zinkwazi/traffic-pcb-sb/software/esp-firmware/components/api_connect/test/resources/data_north_add_V2_0_0.csv

{https://bearanvil.com/current_data/data_north_V1_0_5.csv}
1 | 100
2 | 99
3 | 98
