zinkwazi/traffic-pcb-sb/software/server-software/test_data/missing_num.csv

LED Number | Freeway | Direction | Longitude | Latitude | Tile | openLr Code | Free Flow Speed | Reference
1 | 101 | North | 34.45745 | -119.980356 | 22/699279/1669046 | C6qyXxh+xwo7dOUMBr0KCA== | 72
1 | 101 | South | 34.45657 | -119.975818 | 22/699332/1669058 | C6qqoBiBTgooUhIs+XoKGg== | 73
2 | 101 | North | 34.440808 | -119.942794 | 22/699717/1669281 | C6q6qhh8Xwo5TO40BSkKCw== | 72
2 | 101 | South | 34.438392 | -119.928052 | 22/699888/1669315 | C6qzGBh+QwoqUxPP+5UKFw== | 73
3 | 101 | North | 0 | 0 | 0 | 0 | 0 | 2
3 | 101 | South | 0 | 0 | 0 | 0 | 0 | 2
4 | 101 | North | 34.432527 | -119.890335 | 22/700328/1669398 | C6rCBxh8lgo2QPA0/4sKCg== | 72
4 | 101 | South | 34.432419 | -119.881319 | 22/700433/1669399 | C6q8Uxh8NAooOg5WARAKFw== | 72
5 | 101 | North | 0 | 0 | 0 | 0 | 0 | 4
5 | 101 | South | 0 | 0 | 0 | 0 | 0 | 4
6 | 101 | North | 34.435107 | -119.86683 | 22/700602/1669361 | C6rErhh9Ewo2F/pO/vMKBg== | 71
6 | 101 | South | 34.437084 | -119.855965 | 22/700728/1669333 | C6rDAhh8swomHwe4AS4KFw== | 70
7 | 101 | North | 34.43822 | -119.846035 | 22/700844/1669317 | C6rJRxh9jQo3KPYi/voKBg== | 68
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
