zinkwazi/traffic-pcb-sb/hardware/kicad/matrix_1.kicad_sch

## KiCad design hardware/kicad/matrix_1.kicad_sch (2025-01-31)

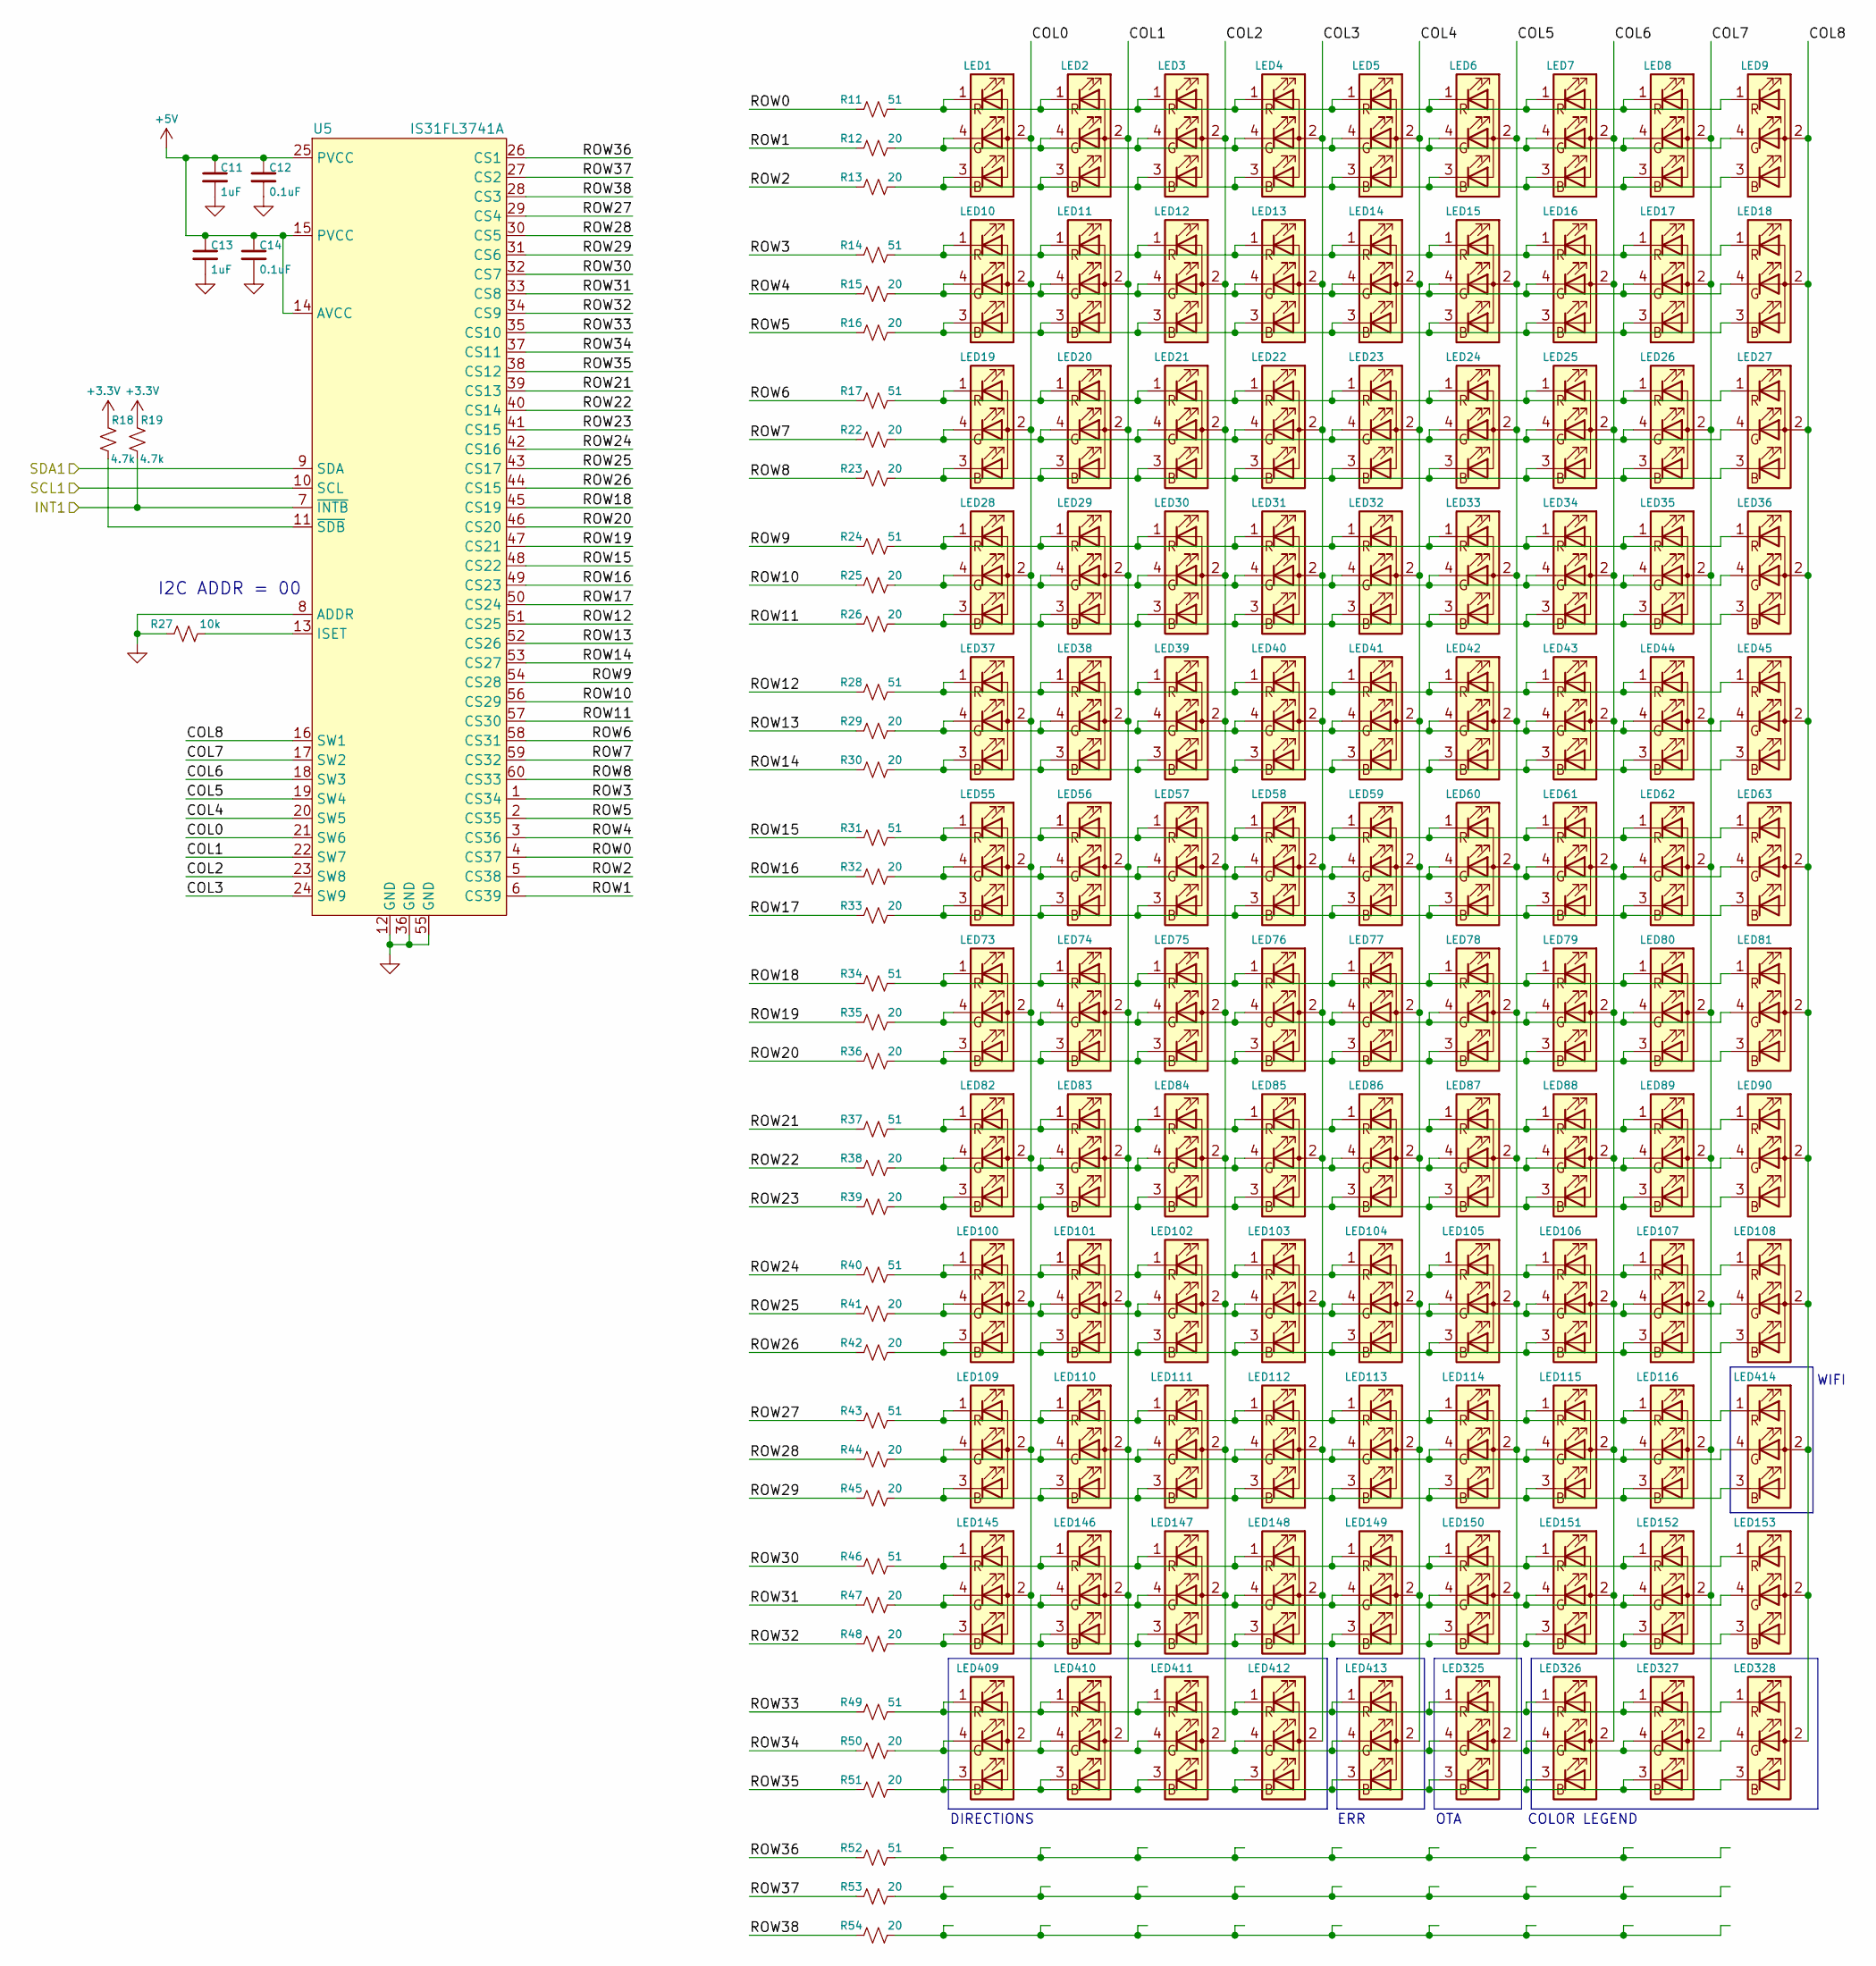
[picture p7: schematic matrix_1.kicad_sch]

Parts:
C11, C13: 1uF; C_0402_1005Metric
C12, C14: 0.1uF; C_0402_1005Metric
LED1, LED2, LED3, LED4, LED5, LED6, LED7, LED8, LED9, LED10, LED11, LED12, LED13, LED14, LED15, LED16, LED17, LED18, LED19, LED20, LED21, LED22, LED23, LED24, LED25, LED26, LED27, LED28, LED29, LED30, LED31, LED32, LED33, LED34, LED35, LED36, LED37, LED38, LED39, LED40, LED41, LED42, LED43, LED44, LED45, LED55, LED56, LED57, LED58, LED59, LED60, LED61, LED62, LED63, LED73, LED74, LED75, LED76, LED77, LED78, LED79, LED80, LED81, LED82, LED83, LED84, LED85, LED86, LED87, LED88, LED89, LED90, LED100, LED101, LED102, LED103, LED104, LED105, LED106, LED107, LED108, LED109, LED110, LED111, LED112, LED113, LED114, LED115, LED116, LED145, LED146, LED147, LED148, LED149, LED150, LED151, LED152, LED153, LED325, LED326, LED327, LED328, LED409, LED410, LED411, LED412, LED413, LED414: LED_ARGB; LED_RGB_0606
R11, R14, R17, R24, R28, R31, R34, R37, R40, R43, R46, R49, R52: 51; R_0402_1005Metric
R12, R13, R15, R16, R22, R23, R25, R26, R29, R30, R32, R33, R35, R36, R38, R39, R41, R42, R44, R45, R47, R48, R50, R51, R53, R54: 20; R_0402_1005Metric
R18, R19: 4.7k; R_0402_1005Metric
R27: 10k; R_0603_1608Metric
U5: IS31FL3741A; QFN40P700X700X80-61N

Connections:
+3.3V: R18.1, R19.1
+5V: C11.1, C12.1, C13.1, C14.1, U5.14 (AVCC), U5.15 (PVCC), U5.25 (PVCC)
COL0: LED1.2 (A), LED10.2 (A), LED19.2 (A), LED28.2 (A), LED37.2 (A), LED55.2 (A), LED73.2 (A), LED82.2 (A), LED100.2 (A), LED109.2 (A), LED145.2 (A), LED409.2 (A), U5.21 (SW6)
COL1: LED2.2 (A), LED11.2 (A), LED20.2 (A), LED29.2 (A), LED38.2 (A), LED56.2 (A), LED74.2 (A), LED83.2 (A), LED101.2 (A), LED110.2 (A), LED146.2 (A), LED410.2 (A), U5.22 (SW7)
COL2: LED3.2 (A), LED12.2 (A), LED21.2 (A), LED30.2 (A), LED39.2 (A), LED57.2 (A), LED75.2 (A), LED84.2 (A), LED102.2 (A), LED111.2 (A), LED147.2 (A), LED411.2 (A), U5.23 (SW8)
COL3: LED4.2 (A), LED13.2 (A), LED22.2 (A), LED31.2 (A), LED40.2 (A), LED58.2 (A), LED76.2 (A), LED85.2 (A), LED103.2 (A), LED112.2 (A), LED148.2 (A), LED412.2 (A), U5.24 (SW9)
COL4: LED5.2 (A), LED14.2 (A), LED23.2 (A), LED32.2 (A), LED41.2 (A), LED59.2 (A), LED77.2 (A), LED86.2 (A), LED104.2 (A), LED113.2 (A), LED149.2 (A), LED413.2 (A), U5.20 (SW5)
COL5: LED6.2 (A), LED15.2 (A), LED24.2 (A), LED33.2 (A), LED42.2 (A), LED60.2 (A), LED78.2 (A), LED87.2 (A), LED105.2 (A), LED114.2 (A), LED150.2 (A), LED325.2 (A), U5.19 (SW4)
COL6: LED7.2 (A), LED16.2 (A), LED25.2 (A), LED34.2 (A), LED43.2 (A), LED61.2 (A), LED79.2 (A), LED88.2 (A), LED106.2 (A), LED115.2 (A), LED151.2 (A), LED326.2 (A), U5.18 (SW3)
COL7: LED8.2 (A), LED17.2 (A), LED26.2 (A), LED35.2 (A), LED44.2 (A), LED62.2 (A), LED80.2 (A), LED89.2 (A), LED107.2 (A), LED116.2 (A), LED152.2 (A), LED327.2 (A), U5.17 (SW2)
COL8: LED9.2 (A), LED18.2 (A), LED27.2 (A), LED36.2 (A), LED45.2 (A), LED63.2 (A), LED81.2 (A), LED90.2 (A), LED108.2 (A), LED153.2 (A), LED328.2 (A), LED414.2 (A), U5.16 (SW1)
GND: C11.2, C12.2, C13.2, C14.2, R27.1, U5.8 (ADDR), U5.12 (GND), U5.36 (GND), U5.55 (GND), U5.61 (GND)
INT1: R19.2, U5.7 (~INTB)
unnamed: LED1.1 (RK), LED2.1 (RK), LED3.1 (RK), LED4.1 (RK), LED5.1 (RK), LED6.1 (RK), LED7.1 (RK), LED8.1 (RK), LED9.1 (RK), R11.2
unnamed: LED1.3 (BK), LED2.3 (BK), LED3.3 (BK), LED4.3 (BK), LED5.3 (BK), LED6.3 (BK), LED7.3 (BK), LED8.3 (BK), LED9.3 (BK), R13.2
unnamed: LED1.4 (GK), LED2.4 (GK), LED3.4 (GK), LED4.4 (GK), LED5.4 (GK), LED6.4 (GK), LED7.4 (GK), LED8.4 (GK), LED9.4 (GK), R12.2
unnamed: LED10.1 (RK), LED11.1 (RK), LED12.1 (RK), LED13.1 (RK), LED14.1 (RK), LED15.1 (RK), LED16.1 (RK), LED17.1 (RK), LED18.1 (RK), R14.2
unnamed: LED10.3 (BK), LED11.3 (BK), LED12.3 (BK), LED13.3 (BK), LED14.3 (BK), LED15.3 (BK), LED16.3 (BK), LED17.3 (BK), LED18.3 (BK), R16.2
unnamed: LED10.4 (GK), LED11.4 (GK), LED12.4 (GK), LED13.4 (GK), LED14.4 (GK), LED15.4 (GK), LED16.4 (GK), LED17.4 (GK), LED18.4 (GK), R15.2
unnamed: LED19.1 (RK), LED20.1 (RK), LED21.1 (RK), LED22.1 (RK), LED23.1 (RK), LED24.1 (RK), LED25.1 (RK), LED26.1 (RK), LED27.1 (RK), R17.2
unnamed: LED19.3 (BK), LED20.3 (BK), LED21.3 (BK), LED22.3 (BK), LED23.3 (BK), LED24.3 (BK), LED25.3 (BK), LED26.3 (BK), LED27.3 (BK), R23.2
unnamed: LED19.4 (GK), LED20.4 (GK), LED21.4 (GK), LED22.4 (GK), LED23.4 (GK), LED24.4 (GK), LED25.4 (GK), LED26.4 (GK), LED27.4 (GK), R22.2
unnamed: LED28.1 (RK), LED29.1 (RK), LED30.1 (RK), LED31.1 (RK), LED32.1 (RK), LED33.1 (RK), LED34.1 (RK), LED35.1 (RK), LED36.1 (RK), R24.2
unnamed: LED28.3 (BK), LED29.3 (BK), LED30.3 (BK), LED31.3 (BK), LED32.3 (BK), LED33.3 (BK), LED34.3 (BK), LED35.3 (BK), LED36.3 (BK), R26.2
unnamed: LED28.4 (GK), LED29.4 (GK), LED30.4 (GK), LED31.4 (GK), LED32.4 (GK), LED33.4 (GK), LED34.4 (GK), LED35.4 (GK), LED36.4 (GK), R25.2
unnamed: LED37.1 (RK), LED38.1 (RK), LED39.1 (RK), LED40.1 (RK), LED41.1 (RK), LED42.1 (RK), LED43.1 (RK), LED44.1 (RK), LED45.1 (RK), R28.2
unnamed: LED37.3 (BK), LED38.3 (BK), LED39.3 (BK), LED40.3 (BK), LED41.3 (BK), LED42.3 (BK), LED43.3 (BK), LED44.3 (BK), LED45.3 (BK), R30.2
unnamed: LED37.4 (GK), LED38.4 (GK), LED39.4 (GK), LED40.4 (GK), LED41.4 (GK), LED42.4 (GK), LED43.4 (GK), LED44.4 (GK), LED45.4 (GK), R29.2
unnamed: LED55.1 (RK), LED56.1 (RK), LED57.1 (RK), LED58.1 (RK), LED59.1 (RK), LED60.1 (RK), LED61.1 (RK), LED62.1 (RK), LED63.1 (RK), R31.2
unnamed: LED55.3 (BK), LED56.3 (BK), LED57.3 (BK), LED58.3 (BK), LED59.3 (BK), LED60.3 (BK), LED61.3 (BK), LED62.3 (BK), LED63.3 (BK), R33.2
unnamed: LED55.4 (GK), LED56.4 (GK), LED57.4 (GK), LED58.4 (GK), LED59.4 (GK), LED60.4 (GK), LED61.4 (GK), LED62.4 (GK), LED63.4 (GK), R32.2
unnamed: LED73.1 (RK), LED74.1 (RK), LED75.1 (RK), LED76.1 (RK), LED77.1 (RK), LED78.1 (RK), LED79.1 (RK), LED80.1 (RK), LED81.1 (RK), R34.2
unnamed: LED73.3 (BK), LED74.3 (BK), LED75.3 (BK), LED76.3 (BK), LED77.3 (BK), LED78.3 (BK), LED79.3 (BK), LED80.3 (BK), LED81.3 (BK), R36.2
unnamed: LED73.4 (GK), LED74.4 (GK), LED75.4 (GK), LED76.4 (GK), LED77.4 (GK), LED78.4 (GK), LED79.4 (GK), LED80.4 (GK), LED81.4 (GK), R35.2
unnamed: LED82.1 (RK), LED83.1 (RK), LED84.1 (RK), LED85.1 (RK), LED86.1 (RK), LED87.1 (RK), LED88.1 (RK), LED89.1 (RK), LED90.1 (RK), R37.2
unnamed: LED82.3 (BK), LED83.3 (BK), LED84.3 (BK), LED85.3 (BK), LED86.3 (BK), LED87.3 (BK), LED88.3 (BK), LED89.3 (BK), LED90.3 (BK), R39.2
unnamed: LED82.4 (GK), LED83.4 (GK), LED84.4 (GK), LED85.4 (GK), LED86.4 (GK), LED87.4 (GK), LED88.4 (GK), LED89.4 (GK), LED90.4 (GK), R38.2
unnamed: LED100.1 (RK), LED101.1 (RK), LED102.1 (RK), LED103.1 (RK), LED104.1 (RK), LED105.1 (RK), LED106.1 (RK), LED107.1 (RK), LED108.1 (RK), R40.2
unnamed: LED100.3 (BK), LED101.3 (BK), LED102.3 (BK), LED103.3 (BK), LED104.3 (BK), LED105.3 (BK), LED106.3 (BK), LED107.3 (BK), LED108.3 (BK), R42.2
unnamed: LED100.4 (GK), LED101.4 (GK), LED102.4 (GK), LED103.4 (GK), LED104.4 (GK), LED105.4 (GK), LED106.4 (GK), LED107.4 (GK), LED108.4 (GK), R41.2
unnamed: LED109.1 (RK), LED110.1 (RK), LED111.1 (RK), LED112.1 (RK), LED113.1 (RK), LED114.1 (RK), LED115.1 (RK), LED116.1 (RK), LED414.1 (RK), R43.2
unnamed: LED109.3 (BK), LED110.3 (BK), LED111.3 (BK), LED112.3 (BK), LED113.3 (BK), LED114.3 (BK), LED115.3 (BK), LED116.3 (BK), LED414.3 (BK), R45.2
unnamed: LED109.4 (GK), LED110.4 (GK), LED111.4 (GK), LED112.4 (GK), LED113.4 (GK), LED114.4 (GK), LED115.4 (GK), LED116.4 (GK), LED414.4 (GK), R44.2
unnamed: LED145.1 (RK), LED146.1 (RK), LED147.1 (RK), LED148.1 (RK), LED149.1 (RK), LED150.1 (RK), LED151.1 (RK), LED152.1 (RK), LED153.1 (RK), R46.2
unnamed: LED145.3 (BK), LED146.3 (BK), LED147.3 (BK), LED148.3 (BK), LED149.3 (BK), LED150.3 (BK), LED151.3 (BK), LED152.3 (BK), LED153.3 (BK), R48.2
unnamed: LED145.4 (GK), LED146.4 (GK), LED147.4 (GK), LED148.4 (GK), LED149.4 (GK), LED150.4 (GK), LED151.4 (GK), LED152.4 (GK), LED153.4 (GK), R47.2
unnamed: LED325.1 (RK), LED326.1 (RK), LED327.1 (RK), LED328.1 (RK), LED409.1 (RK), LED410.1 (RK), LED411.1 (RK), LED412.1 (RK), LED413.1 (RK), R49.2
unnamed: LED325.3 (BK), LED326.3 (BK), LED327.3 (BK), LED328.3 (BK), LED409.3 (BK), LED410.3 (BK), LED411.3 (BK), LED412.3 (BK), LED413.3 (BK), R51.2
unnamed: LED325.4 (GK), LED326.4 (GK), LED327.4 (GK), LED328.4 (GK), LED409.4 (GK), LED410.4 (GK), LED411.4 (GK), LED412.4 (GK), LED413.4 (GK), R50.2
unnamed: R18.2, U5.11 (~SDB)
unnamed: R27.2, U5.13 (ISET)
ROW0: R11.1, U5.4 (CS37)
ROW1: R12.1, U5.6 (CS39)
ROW2: R13.1, U5.5 (CS38)
ROW3: R14.1, U5.1 (CS34)
ROW4: R15.1, U5.3 (CS36)
ROW5: R16.1, U5.2 (CS35)
ROW6: R17.1, U5.58 (CS31)
ROW7: R22.1, U5.59 (CS32)
ROW8: R23.1, U5.60 (CS33)
ROW9: R24.1, U5.54 (CS28)
ROW10: R25.1, U5.56 (CS29)
ROW11: R26.1, U5.57 (CS30)
ROW12: R28.1, U5.51 (CS25)
ROW13: R29.1, U5.52 (CS26)
ROW14: R30.1, U5.53 (CS27)
ROW15: R31.1, U5.48 (CS22)
ROW16: R32.1, U5.49 (CS23)
ROW17: R33.1, U5.50 (CS24)
ROW18: R34.1, U5.45 (CS19)
ROW19: R35.1, U5.47 (CS21)
ROW20: R36.1, U5.46 (CS20)
ROW21: R37.1, U5.39 (CS13)
ROW22: R38.1, U5.40 (CS14)
ROW23: R39.1, U5.41 (CS15)
ROW24: R40.1, U5.42 (CS16)
ROW25: R41.1, U5.43 (CS17)
ROW26: R42.1, U5.44 (CS15)
ROW27: R43.1, U5.29 (CS4)
ROW28: R44.1, U5.30 (CS5)
ROW29: R45.1, U5.31 (CS6)
ROW30: R46.1, U5.32 (CS7)
ROW31: R47.1, U5.33 (CS8)
ROW32: R48.1, U5.34 (CS9)
ROW33: R49.1, U5.35 (CS10)
ROW34: R50.1, U5.37 (CS11)
ROW35: R51.1, U5.38 (CS12)
ROW36: R52.1, U5.26 (CS1)
ROW37: R53.1, U5.27 (CS2)
ROW38: R54.1, U5.28 (CS3)
SCL1: U5.10 (SCL)
SDA1: U5.9 (SDA)

Notes on the sheet:
DIRECTIONS
ERR
WIFI
OTA
COLOR LEGEND
I2C ADDR = 00
