zinkwazi/traffic-pcb-sb/hardware/kicad/matrix_2.kicad_sch

## KiCad design hardware/kicad/matrix_2.kicad_sch (2025-01-31)

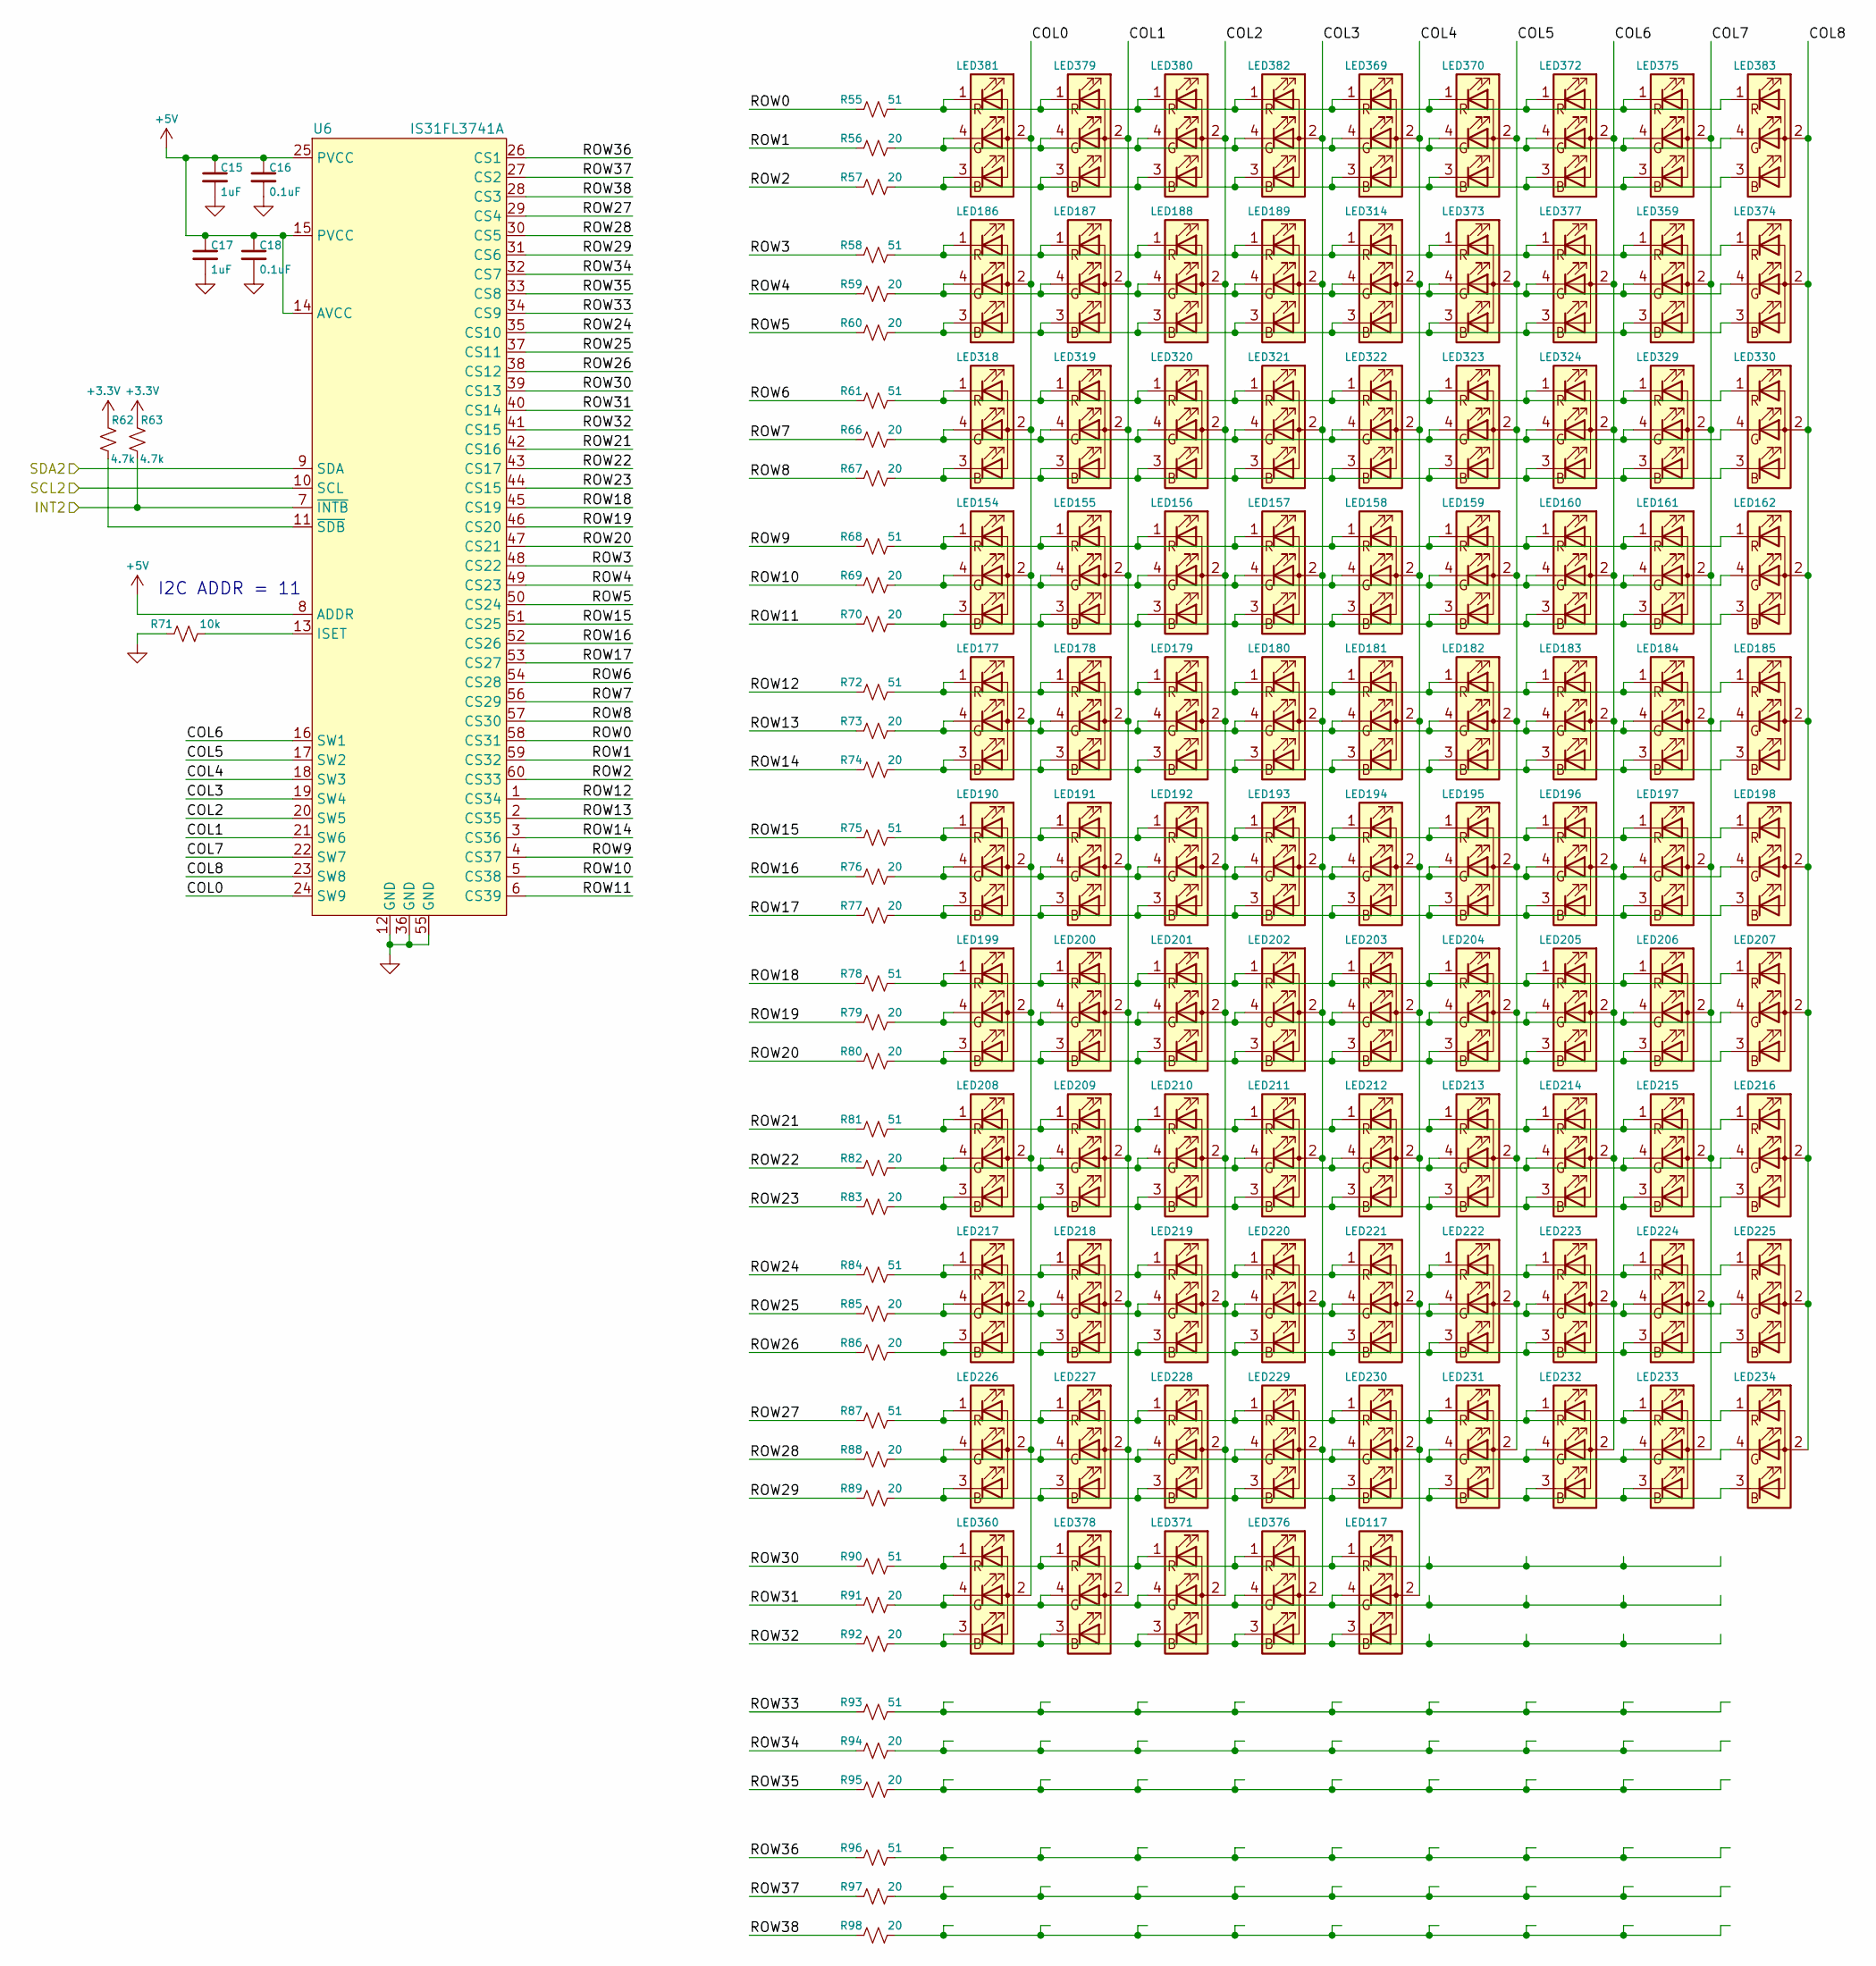
[picture p8: schematic matrix_2.kicad_sch]

Parts:
C15, C17: 1uF; C_0402_1005Metric
C16, C18: 0.1uF; C_0402_1005Metric
LED117, LED154, LED155, LED156, LED157, LED158, LED159, LED160, LED161, LED162, LED177, LED178, LED179, LED180, LED181, LED182, LED183, LED184, LED185, LED186, LED187, LED188, LED189, LED190, LED191, LED192, LED193, LED194, LED195, LED196, LED197, LED198, LED199, LED200, LED201, LED202, LED203, LED204, LED205, LED206, LED207, LED208, LED209, LED210, LED211, LED212, LED213, LED214, LED215, LED216, LED217, LED218, LED219, LED220, LED221, LED222, LED223, LED224, LED225, LED226, LED227, LED228, LED229, LED230, LED231, LED232, LED233, LED234, LED314, LED318, LED319, LED320, LED321, LED322, LED323, LED324, LED329, LED330, LED359, LED360, LED369, LED370, LED371, LED372, LED373, LED374, LED375, LED376, LED377, LED378, LED379, LED380, LED381, LED382, LED383: LED_ARGB; LED_RGB_0606
R55, R58, R61, R68, R72, R75, R78, R81, R84, R87, R90, R93, R96: 51; R_0402_1005Metric
R56, R57, R59, R60, R66, R67, R69, R70, R73, R74, R76, R77, R79, R80, R82, R83, R85, R86, R88, R89, R91, R92, R94, R95, R97, R98: 20; R_0402_1005Metric
R62, R63: 4.7k; R_0402_1005Metric
R71: 10k; R_0603_1608Metric
U6: IS31FL3741A; QFN40P700X700X80-61N

Connections:
+3.3V: R62.1, R63.1
+5V: C15.1, C16.1, C17.1, C18.1, U6.8 (ADDR), U6.14 (AVCC), U6.15 (PVCC), U6.25 (PVCC)
COL0: LED154.2 (A), LED177.2 (A), LED186.2 (A), LED190.2 (A), LED199.2 (A), LED208.2 (A), LED217.2 (A), LED226.2 (A), LED318.2 (A), LED360.2 (A), LED381.2 (A), U6.24 (SW9)
COL1: LED155.2 (A), LED178.2 (A), LED187.2 (A), LED191.2 (A), LED200.2 (A), LED209.2 (A), LED218.2 (A), LED227.2 (A), LED319.2 (A), LED378.2 (A), LED379.2 (A), U6.21 (SW6)
COL2: LED156.2 (A), LED179.2 (A), LED188.2 (A), LED192.2 (A), LED201.2 (A), LED210.2 (A), LED219.2 (A), LED228.2 (A), LED320.2 (A), LED371.2 (A), LED380.2 (A), U6.20 (SW5)
COL3: LED157.2 (A), LED180.2 (A), LED189.2 (A), LED193.2 (A), LED202.2 (A), LED211.2 (A), LED220.2 (A), LED229.2 (A), LED321.2 (A), LED376.2 (A), LED382.2 (A), U6.19 (SW4)
COL4: LED117.2 (A), LED158.2 (A), LED181.2 (A), LED194.2 (A), LED203.2 (A), LED212.2 (A), LED221.2 (A), LED230.2 (A), LED314.2 (A), LED322.2 (A), LED369.2 (A), U6.18 (SW3)
COL5: LED159.2 (A), LED182.2 (A), LED195.2 (A), LED204.2 (A), LED213.2 (A), LED222.2 (A), LED231.2 (A), LED323.2 (A), LED370.2 (A), LED373.2 (A), U6.17 (SW2)
COL6: LED160.2 (A), LED183.2 (A), LED196.2 (A), LED205.2 (A), LED214.2 (A), LED223.2 (A), LED232.2 (A), LED324.2 (A), LED372.2 (A), LED377.2 (A), U6.16 (SW1)
COL7: LED161.2 (A), LED184.2 (A), LED197.2 (A), LED206.2 (A), LED215.2 (A), LED224.2 (A), LED233.2 (A), LED329.2 (A), LED359.2 (A), LED375.2 (A), U6.22 (SW7)
COL8: LED162.2 (A), LED185.2 (A), LED198.2 (A), LED207.2 (A), LED216.2 (A), LED225.2 (A), LED234.2 (A), LED330.2 (A), LED374.2 (A), LED383.2 (A), U6.23 (SW8)
GND: C15.2, C16.2, C17.2, C18.2, R71.1, U6.12 (GND), U6.36 (GND), U6.55 (GND), U6.61 (GND)
INT2: R63.2, U6.7 (~INTB)
unnamed: LED117.1 (RK), LED360.1 (RK), LED371.1 (RK), LED376.1 (RK), LED378.1 (RK), R90.2
unnamed: LED117.3 (BK), LED360.3 (BK), LED371.3 (BK), LED376.3 (BK), LED378.3 (BK), R92.2
unnamed: LED117.4 (GK), LED360.4 (GK), LED371.4 (GK), LED376.4 (GK), LED378.4 (GK), R91.2
unnamed: LED154.1 (RK), LED155.1 (RK), LED156.1 (RK), LED157.1 (RK), LED158.1 (RK), LED159.1 (RK), LED160.1 (RK), LED161.1 (RK), LED162.1 (RK), R68.2
unnamed: LED154.3 (BK), LED155.3 (BK), LED156.3 (BK), LED157.3 (BK), LED158.3 (BK), LED159.3 (BK), LED160.3 (BK), LED161.3 (BK), LED162.3 (BK), R70.2
unnamed: LED154.4 (GK), LED155.4 (GK), LED156.4 (GK), LED157.4 (GK), LED158.4 (GK), LED159.4 (GK), LED160.4 (GK), LED161.4 (GK), LED162.4 (GK), R69.2
unnamed: LED177.1 (RK), LED178.1 (RK), LED179.1 (RK), LED180.1 (RK), LED181.1 (RK), LED182.1 (RK), LED183.1 (RK), LED184.1 (RK), LED185.1 (RK), R72.2
unnamed: LED177.3 (BK), LED178.3 (BK), LED179.3 (BK), LED180.3 (BK), LED181.3 (BK), LED182.3 (BK), LED183.3 (BK), LED184.3 (BK), LED185.3 (BK), R74.2
unnamed: LED177.4 (GK), LED178.4 (GK), LED179.4 (GK), LED180.4 (GK), LED181.4 (GK), LED182.4 (GK), LED183.4 (GK), LED184.4 (GK), LED185.4 (GK), R73.2
unnamed: LED186.1 (RK), LED187.1 (RK), LED188.1 (RK), LED189.1 (RK), LED314.1 (RK), LED359.1 (RK), LED373.1 (RK), LED374.1 (RK), LED377.1 (RK), R58.2
unnamed: LED186.3 (BK), LED187.3 (BK), LED188.3 (BK), LED189.3 (BK), LED314.3 (BK), LED359.3 (BK), LED373.3 (BK), LED374.3 (BK), LED377.3 (BK), R60.2
unnamed: LED186.4 (GK), LED187.4 (GK), LED188.4 (GK), LED189.4 (GK), LED314.4 (GK), LED359.4 (GK), LED373.4 (GK), LED374.4 (GK), LED377.4 (GK), R59.2
unnamed: LED190.1 (RK), LED191.1 (RK), LED192.1 (RK), LED193.1 (RK), LED194.1 (RK), LED195.1 (RK), LED196.1 (RK), LED197.1 (RK), LED198.1 (RK), R75.2
unnamed: LED190.3 (BK), LED191.3 (BK), LED192.3 (BK), LED193.3 (BK), LED194.3 (BK), LED195.3 (BK), LED196.3 (BK), LED197.3 (BK), LED198.3 (BK), R77.2
unnamed: LED190.4 (GK), LED191.4 (GK), LED192.4 (GK), LED193.4 (GK), LED194.4 (GK), LED195.4 (GK), LED196.4 (GK), LED197.4 (GK), LED198.4 (GK), R76.2
unnamed: LED199.1 (RK), LED200.1 (RK), LED201.1 (RK), LED202.1 (RK), LED203.1 (RK), LED204.1 (RK), LED205.1 (RK), LED206.1 (RK), LED207.1 (RK), R78.2
unnamed: LED199.3 (BK), LED200.3 (BK), LED201.3 (BK), LED202.3 (BK), LED203.3 (BK), LED204.3 (BK), LED205.3 (BK), LED206.3 (BK), LED207.3 (BK), R80.2
unnamed: LED199.4 (GK), LED200.4 (GK), LED201.4 (GK), LED202.4 (GK), LED203.4 (GK), LED204.4 (GK), LED205.4 (GK), LED206.4 (GK), LED207.4 (GK), R79.2
unnamed: LED208.1 (RK), LED209.1 (RK), LED210.1 (RK), LED211.1 (RK), LED212.1 (RK), LED213.1 (RK), LED214.1 (RK), LED215.1 (RK), LED216.1 (RK), R81.2
unnamed: LED208.3 (BK), LED209.3 (BK), LED210.3 (BK), LED211.3 (BK), LED212.3 (BK), LED213.3 (BK), LED214.3 (BK), LED215.3 (BK), LED216.3 (BK), R83.2
unnamed: LED208.4 (GK), LED209.4 (GK), LED210.4 (GK), LED211.4 (GK), LED212.4 (GK), LED213.4 (GK), LED214.4 (GK), LED215.4 (GK), LED216.4 (GK), R82.2
unnamed: LED217.1 (RK), LED218.1 (RK), LED219.1 (RK), LED220.1 (RK), LED221.1 (RK), LED222.1 (RK), LED223.1 (RK), LED224.1 (RK), LED225.1 (RK), R84.2
unnamed: LED217.3 (BK), LED218.3 (BK), LED219.3 (BK), LED220.3 (BK), LED221.3 (BK), LED222.3 (BK), LED223.3 (BK), LED224.3 (BK), LED225.3 (BK), R86.2
unnamed: LED217.4 (GK), LED218.4 (GK), LED219.4 (GK), LED220.4 (GK), LED221.4 (GK), LED222.4 (GK), LED223.4 (GK), LED224.4 (GK), LED225.4 (GK), R85.2
unnamed: LED226.1 (RK), LED227.1 (RK), LED228.1 (RK), LED229.1 (RK), LED230.1 (RK), LED231.1 (RK), LED232.1 (RK), LED233.1 (RK), LED234.1 (RK), R87.2
unnamed: LED226.3 (BK), LED227.3 (BK), LED228.3 (BK), LED229.3 (BK), LED230.3 (BK), LED231.3 (BK), LED232.3 (BK), LED233.3 (BK), LED234.3 (BK), R89.2
unnamed: LED226.4 (GK), LED227.4 (GK), LED228.4 (GK), LED229.4 (GK), LED230.4 (GK), LED231.4 (GK), LED232.4 (GK), LED233.4 (GK), LED234.4 (GK), R88.2
unnamed: LED318.1 (RK), LED319.1 (RK), LED320.1 (RK), LED321.1 (RK), LED322.1 (RK), LED323.1 (RK), LED324.1 (RK), LED329.1 (RK), LED330.1 (RK), R61.2
unnamed: LED318.3 (BK), LED319.3 (BK), LED320.3 (BK), LED321.3 (BK), LED322.3 (BK), LED323.3 (BK), LED324.3 (BK), LED329.3 (BK), LED330.3 (BK), R67.2
unnamed: LED318.4 (GK), LED319.4 (GK), LED320.4 (GK), LED321.4 (GK), LED322.4 (GK), LED323.4 (GK), LED324.4 (GK), LED329.4 (GK), LED330.4 (GK), R66.2
unnamed: LED369.1 (RK), LED370.1 (RK), LED372.1 (RK), LED375.1 (RK), LED379.1 (RK), LED380.1 (RK), LED381.1 (RK), LED382.1 (RK), LED383.1 (RK), R55.2
unnamed: LED369.3 (BK), LED370.3 (BK), LED372.3 (BK), LED375.3 (BK), LED379.3 (BK), LED380.3 (BK), LED381.3 (BK), LED382.3 (BK), LED383.3 (BK), R57.2
unnamed: LED369.4 (GK), LED370.4 (GK), LED372.4 (GK), LED375.4 (GK), LED379.4 (GK), LED380.4 (GK), LED381.4 (GK), LED382.4 (GK), LED383.4 (GK), R56.2
unnamed: R62.2, U6.11 (~SDB)
unnamed: R71.2, U6.13 (ISET)
ROW0: R55.1, U6.58 (CS31)
ROW1: R56.1, U6.59 (CS32)
ROW2: R57.1, U6.60 (CS33)
ROW3: R58.1, U6.48 (CS22)
ROW4: R59.1, U6.49 (CS23)
ROW5: R60.1, U6.50 (CS24)
ROW6: R61.1, U6.54 (CS28)
ROW7: R66.1, U6.56 (CS29)
ROW8: R67.1, U6.57 (CS30)
ROW9: R68.1, U6.4 (CS37)
ROW10: R69.1, U6.5 (CS38)
ROW11: R70.1, U6.6 (CS39)
ROW12: R72.1, U6.1 (CS34)
ROW13: R73.1, U6.2 (CS35)
ROW14: R74.1, U6.3 (CS36)
ROW15: R75.1, U6.51 (CS25)
ROW16: R76.1, U6.52 (CS26)
ROW17: R77.1, U6.53 (CS27)
ROW18: R78.1, U6.45 (CS19)
ROW19: R79.1, U6.46 (CS20)
ROW20: R80.1, U6.47 (CS21)
ROW21: R81.1, U6.42 (CS16)
ROW22: R82.1, U6.43 (CS17)
ROW23: R83.1, U6.44 (CS15)
ROW24: R84.1, U6.35 (CS10)
ROW25: R85.1, U6.37 (CS11)
ROW26: R86.1, U6.38 (CS12)
ROW27: R87.1, U6.29 (CS4)
ROW28: R88.1, U6.30 (CS5)
ROW29: R89.1, U6.31 (CS6)
ROW30: R90.1, U6.39 (CS13)
ROW31: R91.1, U6.40 (CS14)
ROW32: R92.1, U6.41 (CS15)
ROW33: R93.1, U6.34 (CS9)
ROW34: R94.1, U6.32 (CS7)
ROW35: R95.1, U6.33 (CS8)
ROW36: R96.1, U6.26 (CS1)
ROW37: R97.1, U6.27 (CS2)
ROW38: R98.1, U6.28 (CS3)
SCL2: U6.10 (SCL)
SDA2: U6.9 (SDA)

Notes on the sheet:
I2C ADDR = 11
