zinkwazi/traffic-pcb-sb/hardware/kicad/matrix_3.kicad_sch

## KiCad design hardware/kicad/matrix_3.kicad_sch (2025-01-31)

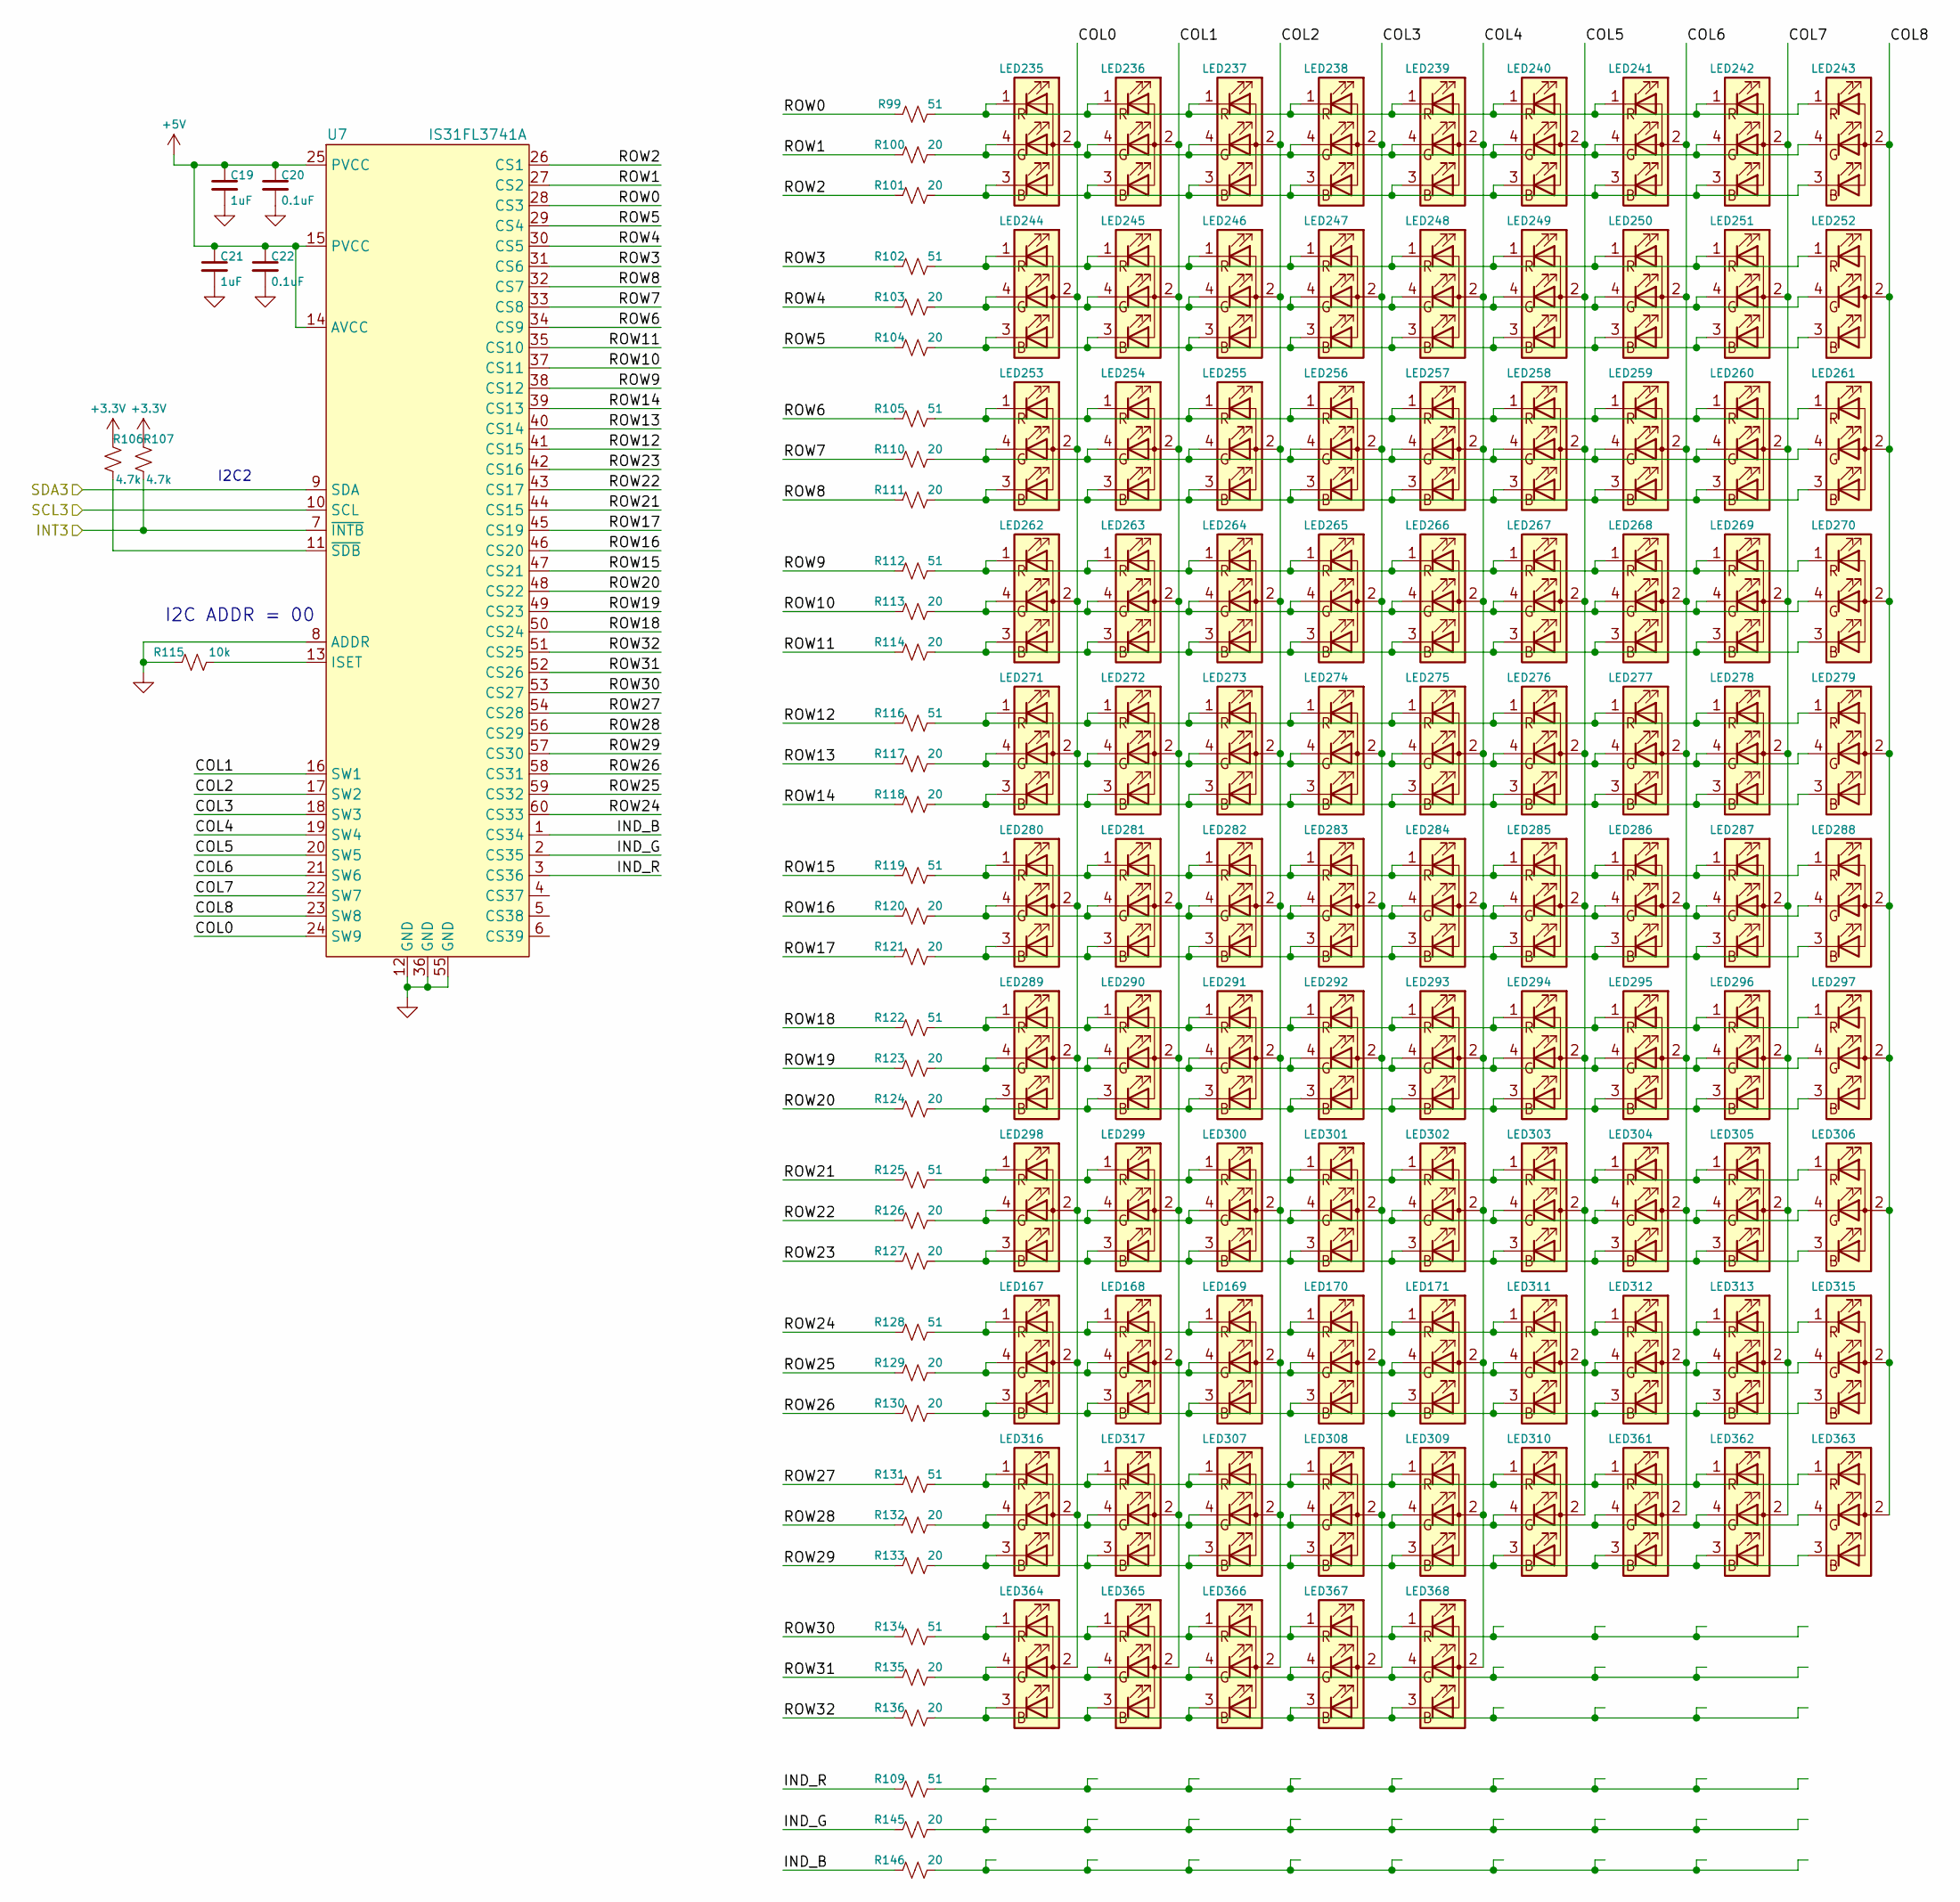
[picture p9: schematic matrix_3.kicad_sch]

Parts:
C19, C21: 1uF; C_0402_1005Metric
C20, C22: 0.1uF; C_0402_1005Metric
LED167, LED168, LED169, LED170, LED171, LED235, LED236, LED237, LED238, LED239, LED240, LED241, LED242, LED243, LED244, LED245, LED246, LED247, LED248, LED249, LED250, LED251, LED252, LED253, LED254, LED255, LED256, LED257, LED258, LED259, LED260, LED261, LED262, LED263, LED264, LED265, LED266, LED267, LED268, LED269, LED270, LED271, LED272, LED273, LED274, LED275, LED276, LED277, LED278, LED279, LED280, LED281, LED282, LED283, LED284, LED285, LED286, LED287, LED288, LED289, LED290, LED291, LED292, LED293, LED294, LED295, LED296, LED297, LED298, LED299, LED300, LED301, LED302, LED303, LED304, LED305, LED306, LED307, LED308, LED309, LED310, LED311, LED312, LED313, LED315, LED316, LED317, LED361, LED362, LED363, LED364, LED365, LED366, LED367, LED368: LED_ARGB; LED_RGB_0606
R99, R102, R105, R109, R112, R116, R119, R122, R125, R128, R131, R134: 51; R_0402_1005Metric
R100, R101, R103, R104, R110, R111, R113, R114, R117, R118, R120, R121, R123, R124, R126, R127, R129, R130, R132, R133, R135, R136, R145, R146: 20; R_0402_1005Metric
R106, R107: 4.7k; R_0402_1005Metric
R115: 10k; R_0603_1608Metric
U7: IS31FL3741A; QFN40P700X700X80-61N

Connections:
+3.3V: R106.1, R107.1
+5V: C19.1, C20.1, C21.1, C22.1, U7.14 (AVCC), U7.15 (PVCC), U7.25 (PVCC)
COL0: LED167.2 (A), LED235.2 (A), LED244.2 (A), LED253.2 (A), LED262.2 (A), LED271.2 (A), LED280.2 (A), LED289.2 (A), LED298.2 (A), LED316.2 (A), LED364.2 (A), U7.24 (SW9)
COL1: LED168.2 (A), LED236.2 (A), LED245.2 (A), LED254.2 (A), LED263.2 (A), LED272.2 (A), LED281.2 (A), LED290.2 (A), LED299.2 (A), LED317.2 (A), LED365.2 (A), U7.16 (SW1)
COL2: LED169.2 (A), LED237.2 (A), LED246.2 (A), LED255.2 (A), LED264.2 (A), LED273.2 (A), LED282.2 (A), LED291.2 (A), LED300.2 (A), LED307.2 (A), LED366.2 (A), U7.17 (SW2)
COL3: LED170.2 (A), LED238.2 (A), LED247.2 (A), LED256.2 (A), LED265.2 (A), LED274.2 (A), LED283.2 (A), LED292.2 (A), LED301.2 (A), LED308.2 (A), LED367.2 (A), U7.18 (SW3)
COL4: LED171.2 (A), LED239.2 (A), LED248.2 (A), LED257.2 (A), LED266.2 (A), LED275.2 (A), LED284.2 (A), LED293.2 (A), LED302.2 (A), LED309.2 (A), LED368.2 (A), U7.19 (SW4)
COL5: LED240.2 (A), LED249.2 (A), LED258.2 (A), LED267.2 (A), LED276.2 (A), LED285.2 (A), LED294.2 (A), LED303.2 (A), LED310.2 (A), LED311.2 (A), U7.20 (SW5)
COL6: LED241.2 (A), LED250.2 (A), LED259.2 (A), LED268.2 (A), LED277.2 (A), LED286.2 (A), LED295.2 (A), LED304.2 (A), LED312.2 (A), LED361.2 (A), U7.21 (SW6)
COL7: LED242.2 (A), LED251.2 (A), LED260.2 (A), LED269.2 (A), LED278.2 (A), LED287.2 (A), LED296.2 (A), LED305.2 (A), LED313.2 (A), LED362.2 (A), U7.22 (SW7)
COL8: LED243.2 (A), LED252.2 (A), LED261.2 (A), LED270.2 (A), LED279.2 (A), LED288.2 (A), LED297.2 (A), LED306.2 (A), LED315.2 (A), LED363.2 (A), U7.23 (SW8)
GND: C19.2, C20.2, C21.2, C22.2, R115.1, U7.8 (ADDR), U7.12 (GND), U7.36 (GND), U7.55 (GND), U7.61 (GND)
IND_B: R146.1, U7.1 (CS34)
IND_G: R145.1, U7.2 (CS35)
IND_R: R109.1, U7.3 (CS36)
INT3: R107.2, U7.7 (~INTB)
unnamed: LED167.1 (RK), LED168.1 (RK), LED169.1 (RK), LED170.1 (RK), LED171.1 (RK), LED311.1 (RK), LED312.1 (RK), LED313.1 (RK), LED315.1 (RK), R128.2
unnamed: LED167.3 (BK), LED168.3 (BK), LED169.3 (BK), LED170.3 (BK), LED171.3 (BK), LED311.3 (BK), LED312.3 (BK), LED313.3 (BK), LED315.3 (BK), R130.2
unnamed: LED167.4 (GK), LED168.4 (GK), LED169.4 (GK), LED170.4 (GK), LED171.4 (GK), LED311.4 (GK), LED312.4 (GK), LED313.4 (GK), LED315.4 (GK), R129.2
unnamed: LED235.1 (RK), LED236.1 (RK), LED237.1 (RK), LED238.1 (RK), LED239.1 (RK), LED240.1 (RK), LED241.1 (RK), LED242.1 (RK), LED243.1 (RK), R99.2
unnamed: LED235.3 (BK), LED236.3 (BK), LED237.3 (BK), LED238.3 (BK), LED239.3 (BK), LED240.3 (BK), LED241.3 (BK), LED242.3 (BK), LED243.3 (BK), R101.2
unnamed: LED235.4 (GK), LED236.4 (GK), LED237.4 (GK), LED238.4 (GK), LED239.4 (GK), LED240.4 (GK), LED241.4 (GK), LED242.4 (GK), LED243.4 (GK), R100.2
unnamed: LED244.1 (RK), LED245.1 (RK), LED246.1 (RK), LED247.1 (RK), LED248.1 (RK), LED249.1 (RK), LED250.1 (RK), LED251.1 (RK), LED252.1 (RK), R102.2
unnamed: LED244.3 (BK), LED245.3 (BK), LED246.3 (BK), LED247.3 (BK), LED248.3 (BK), LED249.3 (BK), LED250.3 (BK), LED251.3 (BK), LED252.3 (BK), R104.2
unnamed: LED244.4 (GK), LED245.4 (GK), LED246.4 (GK), LED247.4 (GK), LED248.4 (GK), LED249.4 (GK), LED250.4 (GK), LED251.4 (GK), LED252.4 (GK), R103.2
unnamed: LED253.1 (RK), LED254.1 (RK), LED255.1 (RK), LED256.1 (RK), LED257.1 (RK), LED258.1 (RK), LED259.1 (RK), LED260.1 (RK), LED261.1 (RK), R105.2
unnamed: LED253.3 (BK), LED254.3 (BK), LED255.3 (BK), LED256.3 (BK), LED257.3 (BK), LED258.3 (BK), LED259.3 (BK), LED260.3 (BK), LED261.3 (BK), R111.2
unnamed: LED253.4 (GK), LED254.4 (GK), LED255.4 (GK), LED256.4 (GK), LED257.4 (GK), LED258.4 (GK), LED259.4 (GK), LED260.4 (GK), LED261.4 (GK), R110.2
unnamed: LED262.1 (RK), LED263.1 (RK), LED264.1 (RK), LED265.1 (RK), LED266.1 (RK), LED267.1 (RK), LED268.1 (RK), LED269.1 (RK), LED270.1 (RK), R112.2
unnamed: LED262.3 (BK), LED263.3 (BK), LED264.3 (BK), LED265.3 (BK), LED266.3 (BK), LED267.3 (BK), LED268.3 (BK), LED269.3 (BK), LED270.3 (BK), R114.2
unnamed: LED262.4 (GK), LED263.4 (GK), LED264.4 (GK), LED265.4 (GK), LED266.4 (GK), LED267.4 (GK), LED268.4 (GK), LED269.4 (GK), LED270.4 (GK), R113.2
unnamed: LED271.1 (RK), LED272.1 (RK), LED273.1 (RK), LED274.1 (RK), LED275.1 (RK), LED276.1 (RK), LED277.1 (RK), LED278.1 (RK), LED279.1 (RK), R116.2
unnamed: LED271.3 (BK), LED272.3 (BK), LED273.3 (BK), LED274.3 (BK), LED275.3 (BK), LED276.3 (BK), LED277.3 (BK), LED278.3 (BK), LED279.3 (BK), R118.2
unnamed: LED271.4 (GK), LED272.4 (GK), LED273.4 (GK), LED274.4 (GK), LED275.4 (GK), LED276.4 (GK), LED277.4 (GK), LED278.4 (GK), LED279.4 (GK), R117.2
unnamed: LED280.1 (RK), LED281.1 (RK), LED282.1 (RK), LED283.1 (RK), LED284.1 (RK), LED285.1 (RK), LED286.1 (RK), LED287.1 (RK), LED288.1 (RK), R119.2
unnamed: LED280.3 (BK), LED281.3 (BK), LED282.3 (BK), LED283.3 (BK), LED284.3 (BK), LED285.3 (BK), LED286.3 (BK), LED287.3 (BK), LED288.3 (BK), R121.2
unnamed: LED280.4 (GK), LED281.4 (GK), LED282.4 (GK), LED283.4 (GK), LED284.4 (GK), LED285.4 (GK), LED286.4 (GK), LED287.4 (GK), LED288.4 (GK), R120.2
unnamed: LED289.1 (RK), LED290.1 (RK), LED291.1 (RK), LED292.1 (RK), LED293.1 (RK), LED294.1 (RK), LED295.1 (RK), LED296.1 (RK), LED297.1 (RK), R122.2
unnamed: LED289.3 (BK), LED290.3 (BK), LED291.3 (BK), LED292.3 (BK), LED293.3 (BK), LED294.3 (BK), LED295.3 (BK), LED296.3 (BK), LED297.3 (BK), R124.2
unnamed: LED289.4 (GK), LED290.4 (GK), LED291.4 (GK), LED292.4 (GK), LED293.4 (GK), LED294.4 (GK), LED295.4 (GK), LED296.4 (GK), LED297.4 (GK), R123.2
unnamed: LED298.1 (RK), LED299.1 (RK), LED300.1 (RK), LED301.1 (RK), LED302.1 (RK), LED303.1 (RK), LED304.1 (RK), LED305.1 (RK), LED306.1 (RK), R125.2
unnamed: LED298.3 (BK), LED299.3 (BK), LED300.3 (BK), LED301.3 (BK), LED302.3 (BK), LED303.3 (BK), LED304.3 (BK), LED305.3 (BK), LED306.3 (BK), R127.2
unnamed: LED298.4 (GK), LED299.4 (GK), LED300.4 (GK), LED301.4 (GK), LED302.4 (GK), LED303.4 (GK), LED304.4 (GK), LED305.4 (GK), LED306.4 (GK), R126.2
unnamed: LED307.1 (RK), LED308.1 (RK), LED309.1 (RK), LED310.1 (RK), LED316.1 (RK), LED317.1 (RK), LED361.1 (RK), LED362.1 (RK), LED363.1 (RK), R131.2
unnamed: LED307.3 (BK), LED308.3 (BK), LED309.3 (BK), LED310.3 (BK), LED316.3 (BK), LED317.3 (BK), LED361.3 (BK), LED362.3 (BK), LED363.3 (BK), R133.2
unnamed: LED307.4 (GK), LED308.4 (GK), LED309.4 (GK), LED310.4 (GK), LED316.4 (GK), LED317.4 (GK), LED361.4 (GK), LED362.4 (GK), LED363.4 (GK), R132.2
unnamed: LED364.1 (RK), LED365.1 (RK), LED366.1 (RK), LED367.1 (RK), LED368.1 (RK), R134.2
unnamed: LED364.3 (BK), LED365.3 (BK), LED366.3 (BK), LED367.3 (BK), LED368.3 (BK), R136.2
unnamed: LED364.4 (GK), LED365.4 (GK), LED366.4 (GK), LED367.4 (GK), LED368.4 (GK), R135.2
unnamed: R106.2, U7.11 (~SDB)
unnamed: R115.2, U7.13 (ISET)
ROW0: R99.1, U7.28 (CS3)
ROW1: R100.1, U7.27 (CS2)
ROW2: R101.1, U7.26 (CS1)
ROW3: R102.1, U7.31 (CS6)
ROW4: R103.1, U7.30 (CS5)
ROW5: R104.1, U7.29 (CS4)
ROW6: R105.1, U7.34 (CS9)
ROW7: R110.1, U7.33 (CS8)
ROW8: R111.1, U7.32 (CS7)
ROW9: R112.1, U7.38 (CS12)
ROW10: R113.1, U7.37 (CS11)
ROW11: R114.1, U7.35 (CS10)
ROW12: R116.1, U7.41 (CS15)
ROW13: R117.1, U7.40 (CS14)
ROW14: R118.1, U7.39 (CS13)
ROW15: R119.1, U7.47 (CS21)
ROW16: R120.1, U7.46 (CS20)
ROW17: R121.1, U7.45 (CS19)
ROW18: R122.1, U7.50 (CS24)
ROW19: R123.1, U7.49 (CS23)
ROW20: R124.1, U7.48 (CS22)
ROW21: R125.1, U7.44 (CS15)
ROW22: R126.1, U7.43 (CS17)
ROW23: R127.1, U7.42 (CS16)
ROW24: R128.1, U7.60 (CS33)
ROW25: R129.1, U7.59 (CS32)
ROW26: R130.1, U7.58 (CS31)
ROW27: R131.1, U7.54 (CS28)
ROW28: R132.1, U7.56 (CS29)
ROW29: R133.1, U7.57 (CS30)
ROW30: R134.1, U7.53 (CS27)
ROW31: R135.1, U7.52 (CS26)
ROW32: R136.1, U7.51 (CS25)
SCL3: U7.10 (SCL)
SDA3: U7.9 (SDA)

Notes on the sheet:
I2C2
I2C ADDR = 00
