zinkwazi/traffic-pcb-sb/hardware/kicad/matrix_4.kicad_sch

## KiCad design hardware/kicad/matrix_4.kicad_sch (2025-01-31)

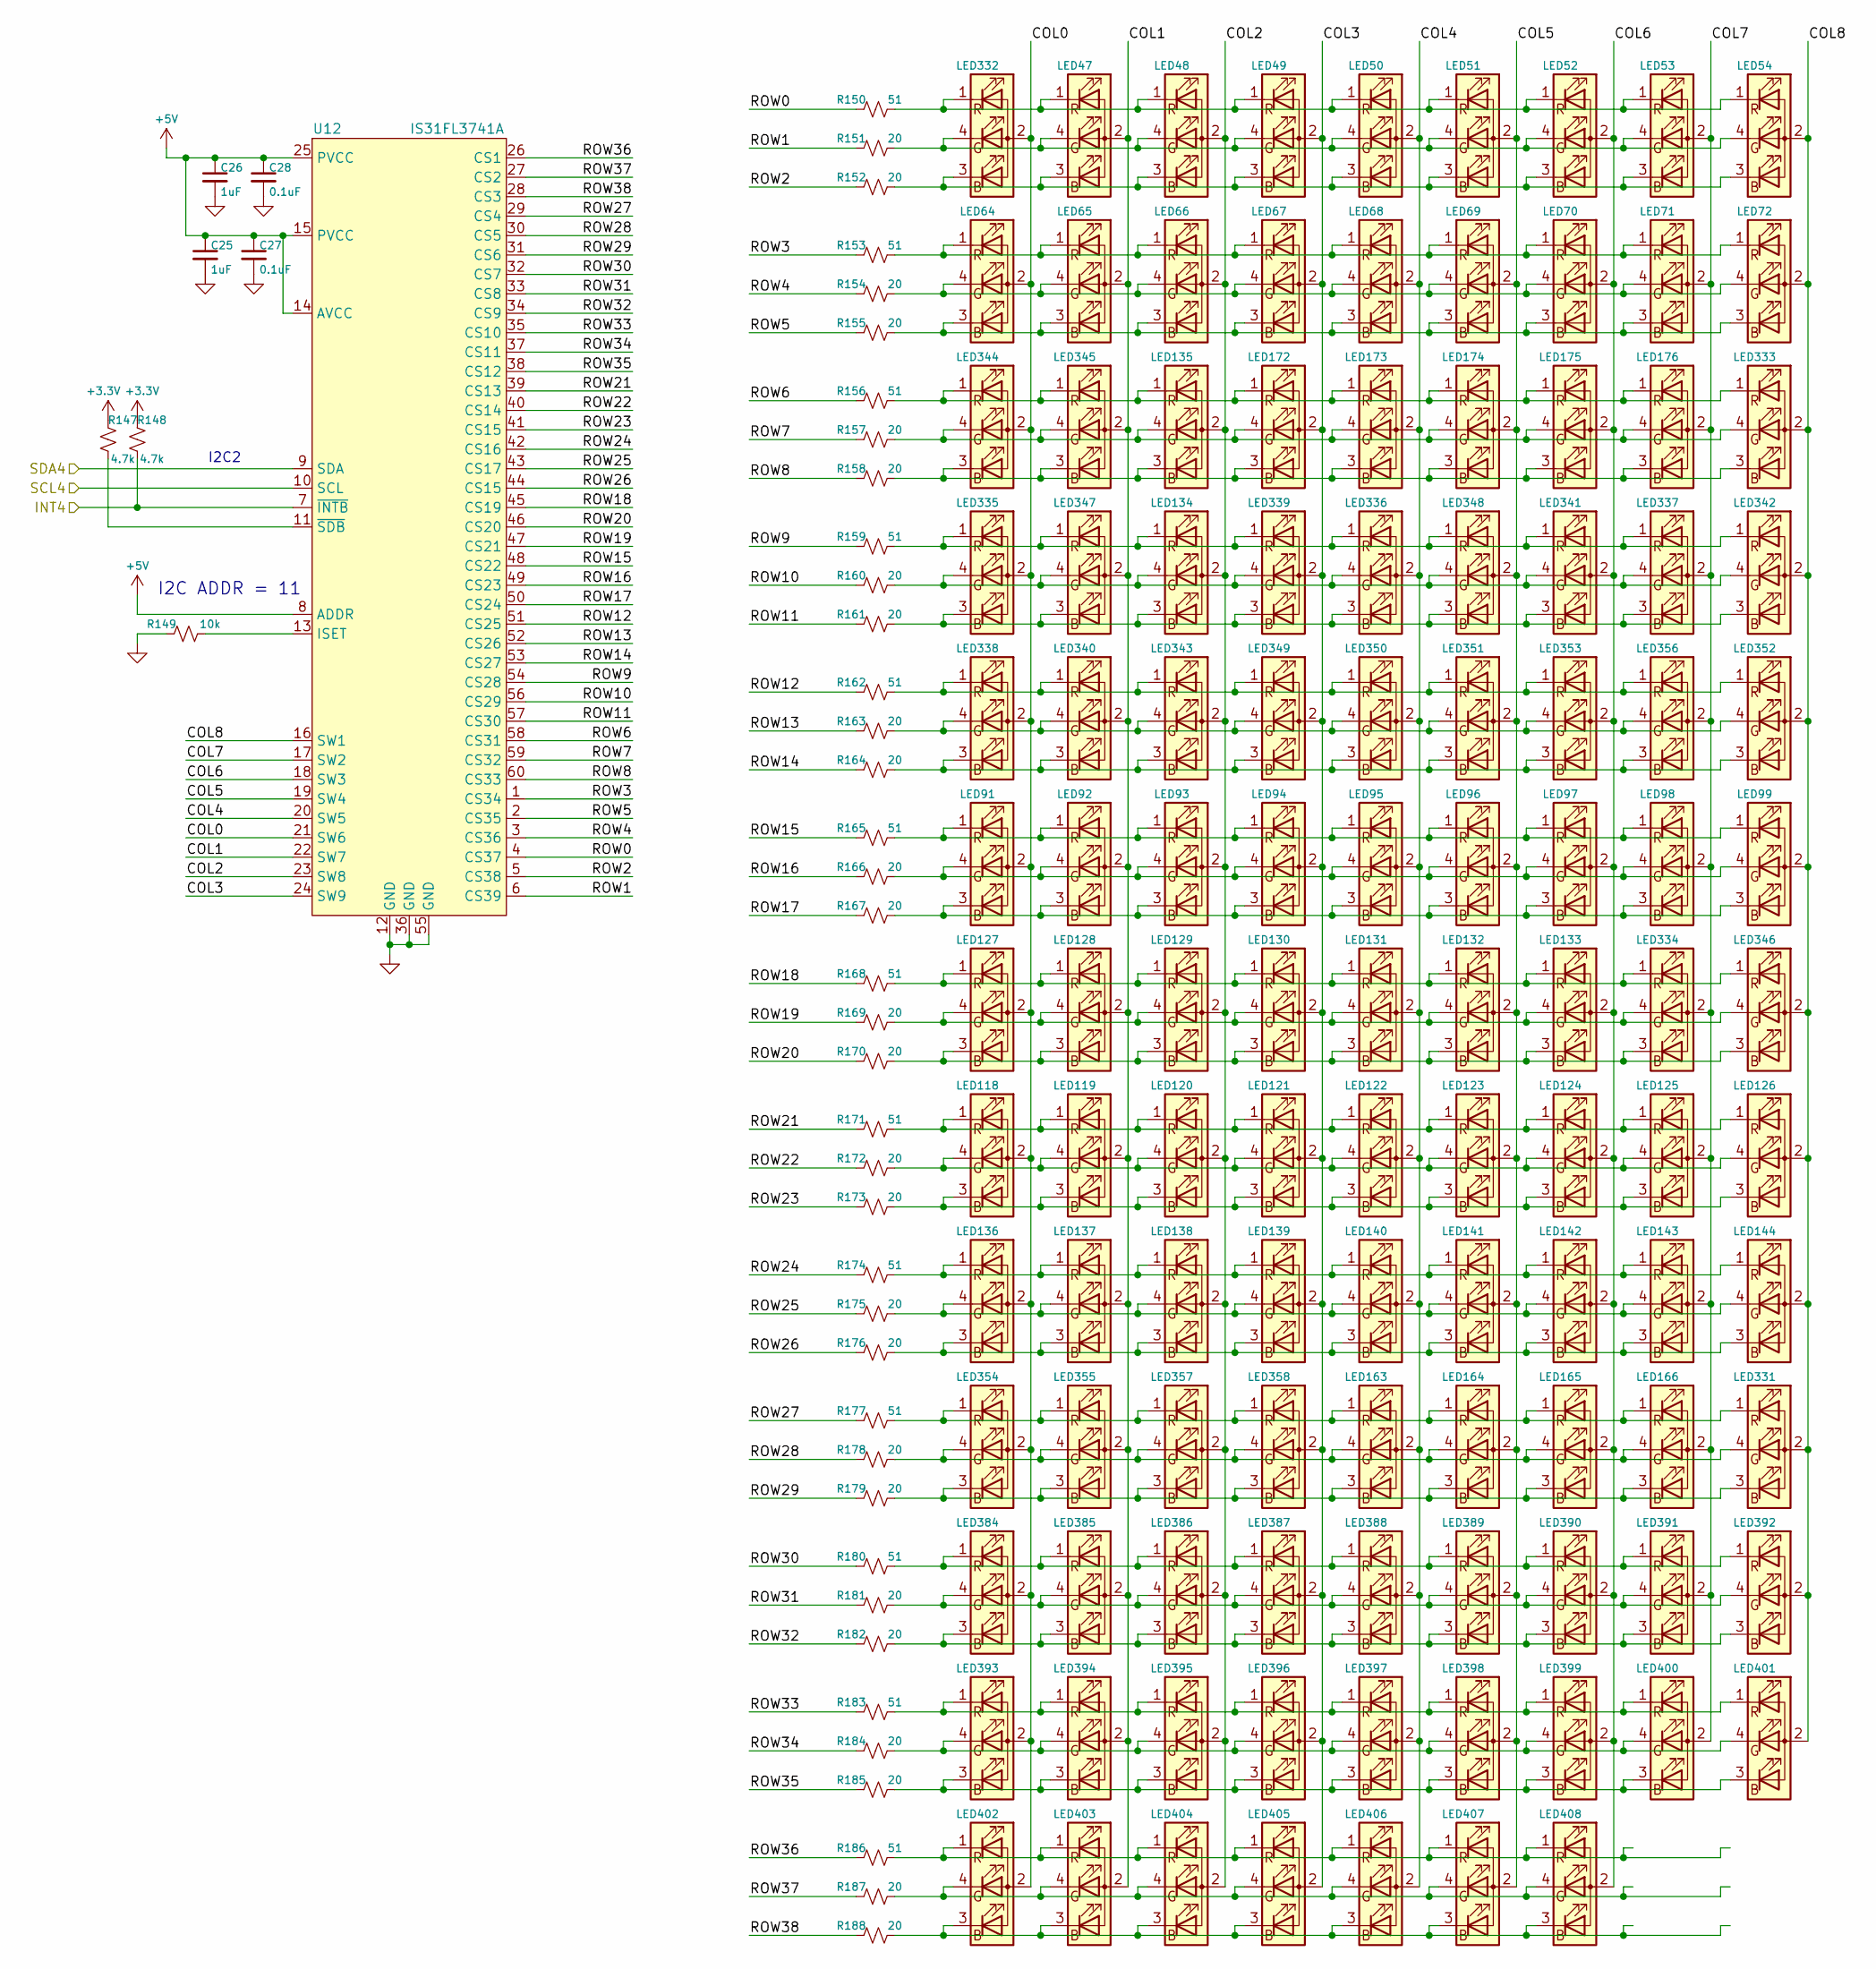
[picture p10: schematic matrix_4.kicad_sch]

Parts:
C25, C26: 1uF; C_0402_1005Metric
C27, C28: 0.1uF; C_0402_1005Metric
LED47, LED48, LED49, LED50, LED51, LED52, LED53, LED54, LED64, LED65, LED66, LED67, LED68, LED69, LED70, LED71, LED72, LED91, LED92, LED93, LED94, LED95, LED96, LED97, LED98, LED99, LED118, LED119, LED120, LED121, LED122, LED123, LED124, LED125, LED126, LED127, LED128, LED129, LED130, LED131, LED132, LED133, LED134, LED135, LED136, LED137, LED138, LED139, LED140, LED141, LED142, LED143, LED144, LED163, LED164, LED165, LED166, LED172, LED173, LED174, LED175, LED176, LED331, LED332, LED333, LED334, LED335, LED336, LED337, LED338, LED339, LED340, LED341, LED342, LED343, LED344, LED345, LED346, LED347, LED348, LED349, LED350, LED351, LED352, LED353, LED354, LED355, LED356, LED357, LED358, LED384, LED385, LED386, LED387, LED388, LED389, LED390, LED391, LED392, LED393, LED394, LED395, LED396, LED397, LED398, LED399, LED400, LED401, LED402, LED403, LED404, LED405, LED406, LED407, LED408: LED_ARGB; LED_RGB_0606
R147, R148: 4.7k; R_0402_1005Metric
R149: 10k; R_0603_1608Metric
R150, R153, R156, R159, R162, R165, R168, R171, R174, R177, R180, R183, R186: 51; R_0402_1005Metric
R151, R152, R154, R155, R157, R158, R160, R161, R163, R164, R166, R167, R169, R170, R172, R173, R175, R176, R178, R179, R181, R182, R184, R185, R187, R188: 20; R_0402_1005Metric
U12: IS31FL3741A; QFN40P700X700X80-61N

Connections:
+3.3V: R147.1, R148.1
+5V: C25.1, C26.1, C27.1, C28.1, U12.8 (ADDR), U12.14 (AVCC), U12.15 (PVCC), U12.25 (PVCC)
COL0: LED64.2 (A), LED91.2 (A), LED118.2 (A), LED127.2 (A), LED136.2 (A), LED332.2 (A), LED335.2 (A), LED338.2 (A), LED344.2 (A), LED354.2 (A), LED384.2 (A), LED393.2 (A), LED402.2 (A), U12.21 (SW6)
COL1: LED47.2 (A), LED65.2 (A), LED92.2 (A), LED119.2 (A), LED128.2 (A), LED137.2 (A), LED340.2 (A), LED345.2 (A), LED347.2 (A), LED355.2 (A), LED385.2 (A), LED394.2 (A), LED403.2 (A), U12.22 (SW7)
COL2: LED48.2 (A), LED66.2 (A), LED93.2 (A), LED120.2 (A), LED129.2 (A), LED134.2 (A), LED135.2 (A), LED138.2 (A), LED343.2 (A), LED357.2 (A), LED386.2 (A), LED395.2 (A), LED404.2 (A), U12.23 (SW8)
COL3: LED49.2 (A), LED67.2 (A), LED94.2 (A), LED121.2 (A), LED130.2 (A), LED139.2 (A), LED172.2 (A), LED339.2 (A), LED349.2 (A), LED358.2 (A), LED387.2 (A), LED396.2 (A), LED405.2 (A), U12.24 (SW9)
COL4: LED50.2 (A), LED68.2 (A), LED95.2 (A), LED122.2 (A), LED131.2 (A), LED140.2 (A), LED163.2 (A), LED173.2 (A), LED336.2 (A), LED350.2 (A), LED388.2 (A), LED397.2 (A), LED406.2 (A), U12.20 (SW5)
COL5: LED51.2 (A), LED69.2 (A), LED96.2 (A), LED123.2 (A), LED132.2 (A), LED141.2 (A), LED164.2 (A), LED174.2 (A), LED348.2 (A), LED351.2 (A), LED389.2 (A), LED398.2 (A), LED407.2 (A), U12.19 (SW4)
COL6: LED52.2 (A), LED70.2 (A), LED97.2 (A), LED124.2 (A), LED133.2 (A), LED142.2 (A), LED165.2 (A), LED175.2 (A), LED341.2 (A), LED353.2 (A), LED390.2 (A), LED399.2 (A), LED408.2 (A), U12.18 (SW3)
COL7: LED53.2 (A), LED71.2 (A), LED98.2 (A), LED125.2 (A), LED143.2 (A), LED166.2 (A), LED176.2 (A), LED334.2 (A), LED337.2 (A), LED356.2 (A), LED391.2 (A), LED400.2 (A), U12.17 (SW2)
COL8: LED54.2 (A), LED72.2 (A), LED99.2 (A), LED126.2 (A), LED144.2 (A), LED331.2 (A), LED333.2 (A), LED342.2 (A), LED346.2 (A), LED352.2 (A), LED392.2 (A), LED401.2 (A), U12.16 (SW1)
GND: C25.2, C26.2, C27.2, C28.2, R149.1, U12.12 (GND), U12.36 (GND), U12.55 (GND), U12.61 (GND)
INT4: R148.2, U12.7 (~INTB)
unnamed: LED64.1 (RK), LED65.1 (RK), LED66.1 (RK), LED67.1 (RK), LED68.1 (RK), LED69.1 (RK), LED70.1 (RK), LED71.1 (RK), LED72.1 (RK), R153.2
unnamed: LED64.3 (BK), LED65.3 (BK), LED66.3 (BK), LED67.3 (BK), LED68.3 (BK), LED69.3 (BK), LED70.3 (BK), LED71.3 (BK), LED72.3 (BK), R155.2
unnamed: LED64.4 (GK), LED65.4 (GK), LED66.4 (GK), LED67.4 (GK), LED68.4 (GK), LED69.4 (GK), LED70.4 (GK), LED71.4 (GK), LED72.4 (GK), R154.2
unnamed: LED91.1 (RK), LED92.1 (RK), LED93.1 (RK), LED94.1 (RK), LED95.1 (RK), LED96.1 (RK), LED97.1 (RK), LED98.1 (RK), LED99.1 (RK), R165.2
unnamed: LED91.3 (BK), LED92.3 (BK), LED93.3 (BK), LED94.3 (BK), LED95.3 (BK), LED96.3 (BK), LED97.3 (BK), LED98.3 (BK), LED99.3 (BK), R167.2
unnamed: LED91.4 (GK), LED92.4 (GK), LED93.4 (GK), LED94.4 (GK), LED95.4 (GK), LED96.4 (GK), LED97.4 (GK), LED98.4 (GK), LED99.4 (GK), R166.2
unnamed: LED118.1 (RK), LED119.1 (RK), LED120.1 (RK), LED121.1 (RK), LED122.1 (RK), LED123.1 (RK), LED124.1 (RK), LED125.1 (RK), LED126.1 (RK), R171.2
unnamed: LED118.3 (BK), LED119.3 (BK), LED120.3 (BK), LED121.3 (BK), LED122.3 (BK), LED123.3 (BK), LED124.3 (BK), LED125.3 (BK), LED126.3 (BK), R173.2
unnamed: LED118.4 (GK), LED119.4 (GK), LED120.4 (GK), LED121.4 (GK), LED122.4 (GK), LED123.4 (GK), LED124.4 (GK), LED125.4 (GK), LED126.4 (GK), R172.2
unnamed: LED127.1 (RK), LED128.1 (RK), LED129.1 (RK), LED130.1 (RK), LED131.1 (RK), LED132.1 (RK), LED133.1 (RK), LED334.1 (RK), LED346.1 (RK), R168.2
unnamed: LED127.3 (BK), LED128.3 (BK), LED129.3 (BK), LED130.3 (BK), LED131.3 (BK), LED132.3 (BK), LED133.3 (BK), LED334.3 (BK), LED346.3 (BK), R170.2
unnamed: LED127.4 (GK), LED128.4 (GK), LED129.4 (GK), LED130.4 (GK), LED131.4 (GK), LED132.4 (GK), LED133.4 (GK), LED334.4 (GK), LED346.4 (GK), R169.2
unnamed: LED134.1 (RK), LED335.1 (RK), LED336.1 (RK), LED337.1 (RK), LED339.1 (RK), LED341.1 (RK), LED342.1 (RK), LED347.1 (RK), LED348.1 (RK), R159.2
unnamed: LED134.3 (BK), LED335.3 (BK), LED336.3 (BK), LED337.3 (BK), LED339.3 (BK), LED341.3 (BK), LED342.3 (BK), LED347.3 (BK), LED348.3 (BK), R161.2
unnamed: LED134.4 (GK), LED335.4 (GK), LED336.4 (GK), LED337.4 (GK), LED339.4 (GK), LED341.4 (GK), LED342.4 (GK), LED347.4 (GK), LED348.4 (GK), R160.2
unnamed: LED135.1 (RK), LED172.1 (RK), LED173.1 (RK), LED174.1 (RK), LED175.1 (RK), LED176.1 (RK), LED333.1 (RK), LED344.1 (RK), LED345.1 (RK), R156.2
unnamed: LED135.3 (BK), LED172.3 (BK), LED173.3 (BK), LED174.3 (BK), LED175.3 (BK), LED176.3 (BK), LED333.3 (BK), LED344.3 (BK), LED345.3 (BK), R158.2
unnamed: LED135.4 (GK), LED172.4 (GK), LED173.4 (GK), LED174.4 (GK), LED175.4 (GK), LED176.4 (GK), LED333.4 (GK), LED344.4 (GK), LED345.4 (GK), R157.2
unnamed: LED136.1 (RK), LED137.1 (RK), LED138.1 (RK), LED139.1 (RK), LED140.1 (RK), LED141.1 (RK), LED142.1 (RK), LED143.1 (RK), LED144.1 (RK), R174.2
unnamed: LED136.3 (BK), LED137.3 (BK), LED138.3 (BK), LED139.3 (BK), LED140.3 (BK), LED141.3 (BK), LED142.3 (BK), LED143.3 (BK), LED144.3 (BK), R176.2
unnamed: LED136.4 (GK), LED137.4 (GK), LED138.4 (GK), LED139.4 (GK), LED140.4 (GK), LED141.4 (GK), LED142.4 (GK), LED143.4 (GK), LED144.4 (GK), R175.2
unnamed: LED163.1 (RK), LED164.1 (RK), LED165.1 (RK), LED166.1 (RK), LED331.1 (RK), LED354.1 (RK), LED355.1 (RK), LED357.1 (RK), LED358.1 (RK), R177.2
unnamed: LED163.3 (BK), LED164.3 (BK), LED165.3 (BK), LED166.3 (BK), LED331.3 (BK), LED354.3 (BK), LED355.3 (BK), LED357.3 (BK), LED358.3 (BK), R179.2
unnamed: LED163.4 (GK), LED164.4 (GK), LED165.4 (GK), LED166.4 (GK), LED331.4 (GK), LED354.4 (GK), LED355.4 (GK), LED357.4 (GK), LED358.4 (GK), R178.2
unnamed: LED47.1 (RK), LED48.1 (RK), LED49.1 (RK), LED50.1 (RK), LED51.1 (RK), LED52.1 (RK), LED53.1 (RK), LED54.1 (RK), LED332.1 (RK), R150.2
unnamed: LED47.3 (BK), LED48.3 (BK), LED49.3 (BK), LED50.3 (BK), LED51.3 (BK), LED52.3 (BK), LED53.3 (BK), LED54.3 (BK), LED332.3 (BK), R152.2
unnamed: LED47.4 (GK), LED48.4 (GK), LED49.4 (GK), LED50.4 (GK), LED51.4 (GK), LED52.4 (GK), LED53.4 (GK), LED54.4 (GK), LED332.4 (GK), R151.2
unnamed: LED338.1 (RK), LED340.1 (RK), LED343.1 (RK), LED349.1 (RK), LED350.1 (RK), LED351.1 (RK), LED352.1 (RK), LED353.1 (RK), LED356.1 (RK), R162.2
unnamed: LED338.3 (BK), LED340.3 (BK), LED343.3 (BK), LED349.3 (BK), LED350.3 (BK), LED351.3 (BK), LED352.3 (BK), LED353.3 (BK), LED356.3 (BK), R164.2
unnamed: LED338.4 (GK), LED340.4 (GK), LED343.4 (GK), LED349.4 (GK), LED350.4 (GK), LED351.4 (GK), LED352.4 (GK), LED353.4 (GK), LED356.4 (GK), R163.2
unnamed: LED384.1 (RK), LED385.1 (RK), LED386.1 (RK), LED387.1 (RK), LED388.1 (RK), LED389.1 (RK), LED390.1 (RK), LED391.1 (RK), LED392.1 (RK), R180.2
unnamed: LED384.3 (BK), LED385.3 (BK), LED386.3 (BK), LED387.3 (BK), LED388.3 (BK), LED389.3 (BK), LED390.3 (BK), LED391.3 (BK), LED392.3 (BK), R182.2
unnamed: LED384.4 (GK), LED385.4 (GK), LED386.4 (GK), LED387.4 (GK), LED388.4 (GK), LED389.4 (GK), LED390.4 (GK), LED391.4 (GK), LED392.4 (GK), R181.2
unnamed: LED393.1 (RK), LED394.1 (RK), LED395.1 (RK), LED396.1 (RK), LED397.1 (RK), LED398.1 (RK), LED399.1 (RK), LED400.1 (RK), LED401.1 (RK), R183.2
unnamed: LED393.3 (BK), LED394.3 (BK), LED395.3 (BK), LED396.3 (BK), LED397.3 (BK), LED398.3 (BK), LED399.3 (BK), LED400.3 (BK), LED401.3 (BK), R185.2
unnamed: LED393.4 (GK), LED394.4 (GK), LED395.4 (GK), LED396.4 (GK), LED397.4 (GK), LED398.4 (GK), LED399.4 (GK), LED400.4 (GK), LED401.4 (GK), R184.2
unnamed: LED402.1 (RK), LED403.1 (RK), LED404.1 (RK), LED405.1 (RK), LED406.1 (RK), LED407.1 (RK), LED408.1 (RK), R186.2
unnamed: LED402.3 (BK), LED403.3 (BK), LED404.3 (BK), LED405.3 (BK), LED406.3 (BK), LED407.3 (BK), LED408.3 (BK), R188.2
unnamed: LED402.4 (GK), LED403.4 (GK), LED404.4 (GK), LED405.4 (GK), LED406.4 (GK), LED407.4 (GK), LED408.4 (GK), R187.2
unnamed: R147.2, U12.11 (~SDB)
unnamed: R149.2, U12.13 (ISET)
ROW0: R150.1, U12.4 (CS37)
ROW1: R151.1, U12.6 (CS39)
ROW2: R152.1, U12.5 (CS38)
ROW3: R153.1, U12.1 (CS34)
ROW4: R154.1, U12.3 (CS36)
ROW5: R155.1, U12.2 (CS35)
ROW6: R156.1, U12.58 (CS31)
ROW7: R157.1, U12.59 (CS32)
ROW8: R158.1, U12.60 (CS33)
ROW9: R159.1, U12.54 (CS28)
ROW10: R160.1, U12.56 (CS29)
ROW11: R161.1, U12.57 (CS30)
ROW12: R162.1, U12.51 (CS25)
ROW13: R163.1, U12.52 (CS26)
ROW14: R164.1, U12.53 (CS27)
ROW15: R165.1, U12.48 (CS22)
ROW16: R166.1, U12.49 (CS23)
ROW17: R167.1, U12.50 (CS24)
ROW18: R168.1, U12.45 (CS19)
ROW19: R169.1, U12.47 (CS21)
ROW20: R170.1, U12.46 (CS20)
ROW21: R171.1, U12.39 (CS13)
ROW22: R172.1, U12.40 (CS14)
ROW23: R173.1, U12.41 (CS15)
ROW24: R174.1, U12.42 (CS16)
ROW25: R175.1, U12.43 (CS17)
ROW26: R176.1, U12.44 (CS15)
ROW27: R177.1, U12.29 (CS4)
ROW28: R178.1, U12.30 (CS5)
ROW29: R179.1, U12.31 (CS6)
ROW30: R180.1, U12.32 (CS7)
ROW31: R181.1, U12.33 (CS8)
ROW32: R182.1, U12.34 (CS9)
ROW33: R183.1, U12.35 (CS10)
ROW34: R184.1, U12.37 (CS11)
ROW35: R185.1, U12.38 (CS12)
ROW36: R186.1, U12.26 (CS1)
ROW37: R187.1, U12.27 (CS2)
ROW38: R188.1, U12.28 (CS3)
SCL4: U12.10 (SCL)
SDA4: U12.9 (SDA)

Notes on the sheet:
I2C2
I2C ADDR = 11
