zinkwazi/traffic-pcb-sb/hardware/kicad/traffic_paradise.kicad_sch

## KiCad design hardware/kicad/traffic_paradise.kicad_sch (2025-01-31)

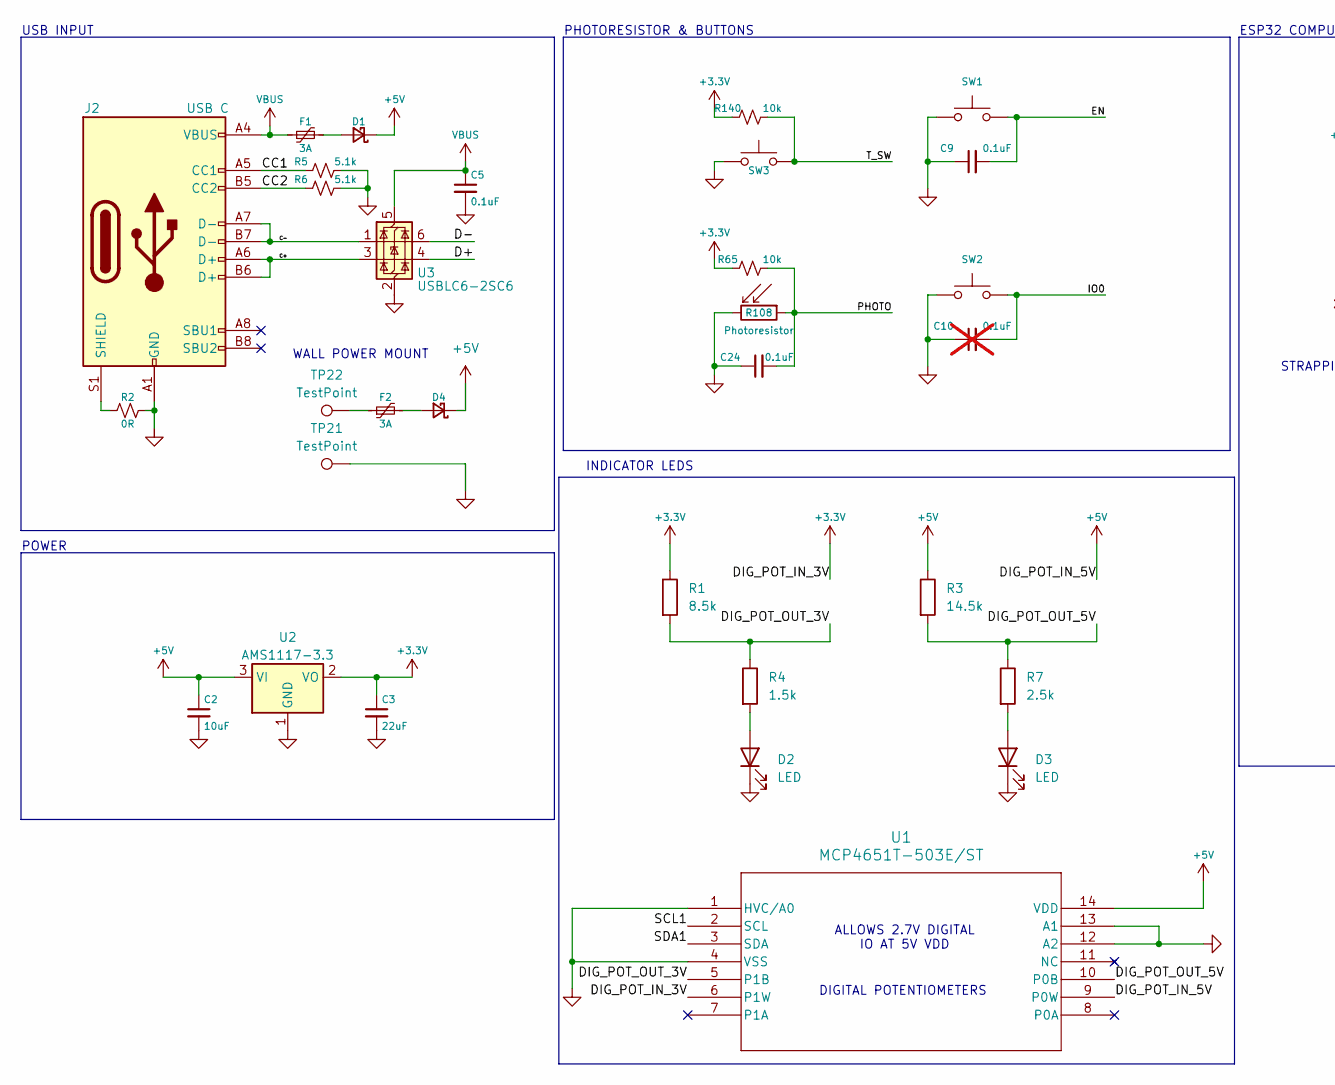
[picture p11: schematic traffic_paradise.kicad_sch, part in row 1, column 1]

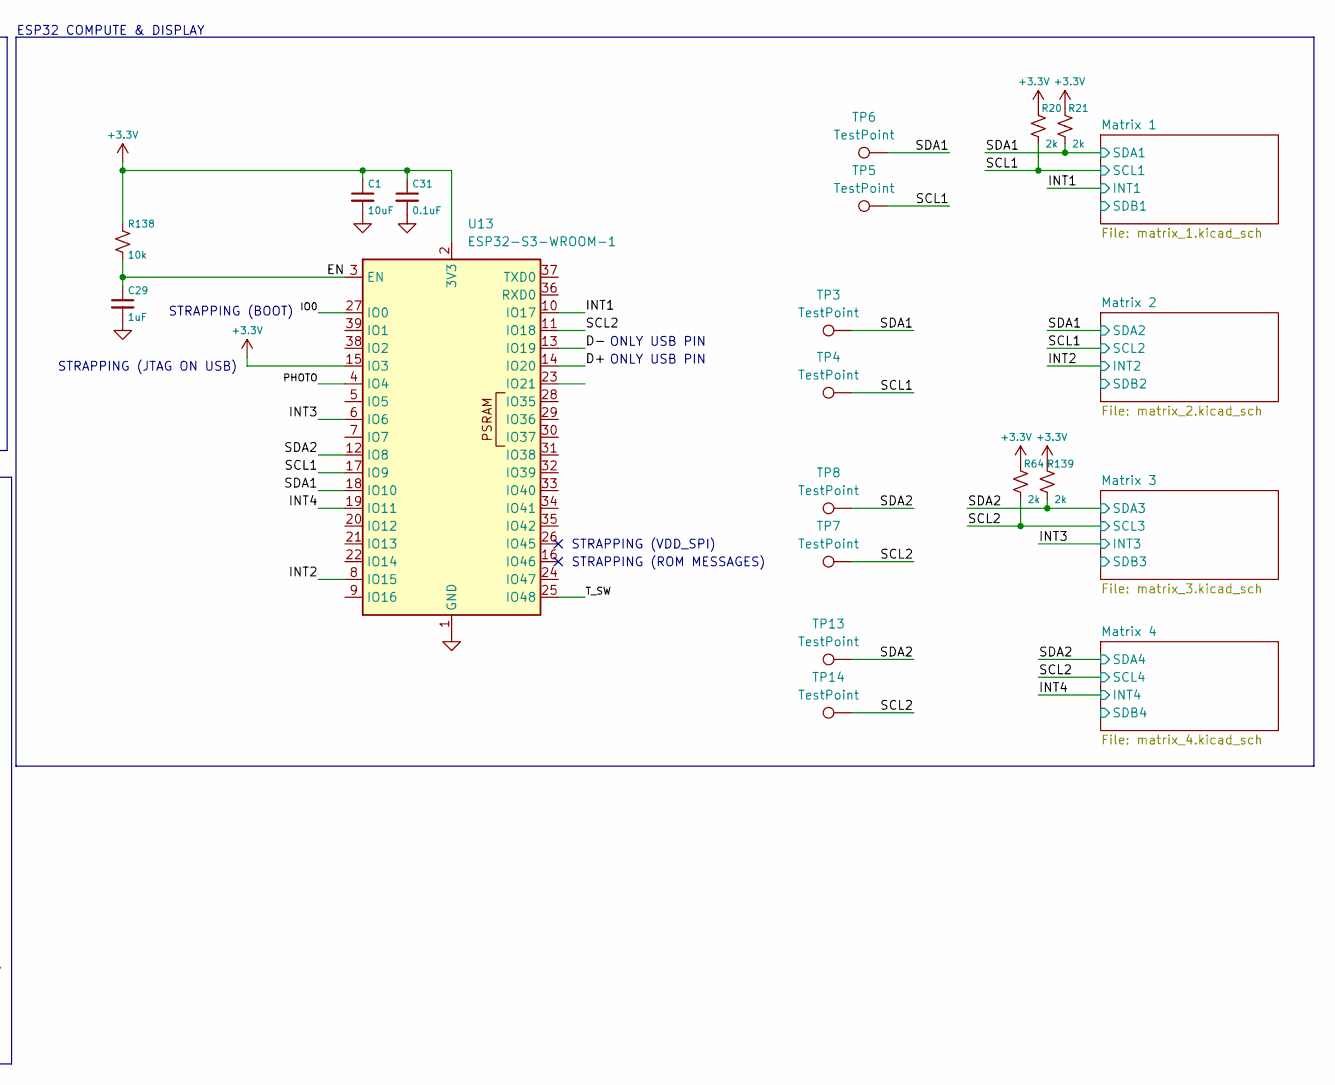
[picture p12: schematic traffic_paradise.kicad_sch, part in row 1, column 2]

Parts:
C1, C2: 10uF; C_0402_1005Metric
C3: 22uF; C_0603_1608Metric
C5, C9, C24, C31: 0.1uF; C_0402_1005Metric
C10: 0.1uF; C_0402_1005Metric; not fitted
C29: 1uF; C_0402_1005Metric
D1, D4: RBR3MM40ATR; DIO_RB051MM_ROM
D2, D3: LED; LED_0805_2012Metric
F1, F2: 3A; Fuse_1206_3216Metric
J2: USB C; USB_C_Receptacle_HRO_TYPE-C-31-M-12
R1: 8.5k; R_0603_1608Metric
R2: 0R; R_0402_1005Metric
R3: 14.5k; R_0603_1608Metric
R4: 1.5k; R_0603_1608Metric
R5, R6: 5.1k; R_0402_1005Metric
R7: 2.5k; R_0603_1608Metric
R20, R21, R64, R139: 2k; R_0402_1005Metric
R65, R138, R140: 10k; R_0402_1005Metric
R108: Photoresistor
SW1, SW2, SW3: SW_Push; SW_SPST_SKQG_WithoutStem
TP3, TP4, TP5, TP6, TP7, TP8, TP13, TP14, TP21, TP22: TestPoint; TestPoint_Pad_D2.5mm
U1: MCP4651T-503E/ST; TSSOP14_MC_MCH
U2: AMS1117-3.3; SOT-223-3_TabPin2
U3: USBLC6-2SC6; SOT-23-6
U13: ESP32-S3-WROOM-1

Connections:
+3.3V: C1.1, C3.1, C31.1, R1.1, R20.1, R21.1, R64.1, R65.1, R138.1, R139.1, R140.1, U1.6 (P1W), U2.2 (VO), U13.2 (3V3), U13.15 (IO3)
+5V: C2.1, D1.1 (K), D4.1 (K), R3.1, U1.9 (P0W), U1.14 (VDD), U2.3 (VI)
C+: J2.A6 (D+), J2.B6 (D+), U3.3 (I/O2)
C-: J2.A7 (D-), J2.B7 (D-), U3.1 (I/O1)
CC1: J2.A5 (CC1), R5.1
CC2: J2.B5 (CC2), R6.1
D+: U3.4 (I/O2), U13.14 (IO20)
D-: U3.6 (I/O1), U13.13 (IO19)
DIG_POT_OUT_3V: R1.2, R4.1, U1.5 (P1B)
DIG_POT_OUT_5V: R3.2, R7.1, U1.10 (P0B)
EN: C9.2, C29.1, R138.2, SW1.2, U13.3 (EN)
GND: C1.2, C2.2, C3.2, C5.2, C9.1, C10.1, C24.1, C29.2, C31.2, D2.1 (K), D3.1 (K), J2.A1 (GND), J2.A12 (GND), J2.B1 (GND), J2.B12 (GND), R2.2, R5.2, R6.2, R108.2, SW1.1, SW2.1, SW3.1, TP21.1, U1.1 (HVC/A0), U1.4 (VSS), U1.12 (A2), U1.13 (A1), U2.1 (GND), U3.2 (GND), U13.1 (GND), U13.40 (GND), U13.41 (GND)
INT1: U13.10 (IO17)
INT2: U13.8 (IO15)
INT3: U13.6 (IO6)
INT4: U13.19 (IO11)
IO0: C10.2, SW2.2, U13.27 (IO0)
unnamed: D1.2 (A), F1.2
unnamed: D2.2 (A), R4.2
unnamed: D3.2 (A), R7.2
unnamed: D4.2 (A), F2.2
unnamed: F2.1, TP22.1
unnamed: J2.S1 (SHIELD), R2.1
PHOTO: C24.2, R65.2, R108.1, U13.4 (IO4)
SCL1: R20.2, TP4.1, TP5.1, U1.2 (SCL), U13.17 (IO9)
SCL2: R64.2, TP7.1, TP14.1, U13.11 (IO18)
SDA1: R21.2, TP3.1, TP6.1, U1.3 (SDA), U13.18 (IO10)
SDA2: R139.2, TP8.1, TP13.1, U13.12 (IO8)
T_SW: R140.2, SW3.2, U13.25 (IO48)
VBUS: C5.1, F1.1, J2.A4 (VBUS), J2.A9 (VBUS), J2.B4 (VBUS), J2.B9 (VBUS), U3.5 (VBUS)

Notes on the sheet:
STRAPPING (BOOT)
USB INPUT
DIGITAL POTENTIOMETERS
INDICATOR LEDS
ONLY USB PIN
WALL POWER MOUNT
PHOTORESISTOR & BUTTONS
ESP32 COMPUTE & DISPLAY
ALLOWS 2.7V DIGITAL IO AT 5V VDD
POWER
STRAPPING (VDD_SPI)
STRAPPING (ROM MESSAGES)
STRAPPING (JTAG ON USB)
