zinkwazi/traffic-pcb-sb/software/esp-firmware/components/input/src/input.c

/**
 * input.c
 * 
 * Contains button input functionality, which
 * is complicated by differences in meaning
 * between quick and long button presses.
 */

#include "input.h"

#include <stdbool.h>

#include "driver/gpio.h"
#include "esp_err.h"
#include "esp_timer.h"
#include "freertos/FreeRTOS.h"
#include "freertos/projdefs.h"
#include "freertos/task.h"
#include "sdkconfig.h"

#include "app_err.h"
#include "input_queue.h"
#include "pinout.h"
#include "refresh.h"

#define TAG "input"

#define DIR_BUTTON_LONG_PRESS_TIME_US 500000

static esp_timer_handle_t dirButtonTimer = NULL;
static esp_timer_handle_t dirButtonDebounceTimer = NULL;
static bool dirButtonShortEnable = false;
static bool dirButtonLongEnable = false;

static esp_err_t initDirectionButton(void);
static esp_err_t initOTAButton(TaskHandle_t otaTask);
static void otaButtonISR(void *params);
static void dirButtonISR(void *params);

static void timerDirButtonCallback(void *params);
static void timerDebounceDirButtonCallback(void *params);

/**
 * Initializes all input buttons on the board.
 * 
 * @param otaTask A handle to the OTA task, which will be used
 * to send it task notifications.
 * @param mainTask A handle to the main task, which will be used
 * to send it task notifications.
 * @param toggle A pointer to a boolean which the main task uses
 * to determine whether to switch the direction of traffic when
 * a task notification is received.
 */
esp_err_t initInput(TaskHandle_t otaTask)
{
    esp_err_t err;

    err = initDirectionButton();
    if (err != ESP_OK) return err;

    err = initOTAButton(otaTask);
    if (err != ESP_OK) return err;
    
    return ESP_OK;
}

/**
 * Quick direction button press.
 * 
 * This button press causes a refresh of the board
 * and switches direction or quickly clears the board 
 * if a refresh is already underway.
 * 
 * @note Due to the presence of the "hold direction press",
 * this button registers when the button is released after
 * a debouncing period.
 */

esp_err_t enableQuickDirButton(void)
{
    esp_err_t err = ESP_OK;
    if ((!dirButtonShortEnable) && (!dirButtonLongEnable))
    {
        /* interrupt is disabled, thus enable it */
        dirButtonShortEnable = true;
        err = gpio_intr_enable(T_SW_PIN);
    } else
    {
        dirButtonShortEnable = true;
    }
    return err;
}

esp_err_t disableQuickDirButton(void)
{
    esp_err_t err = ESP_OK;
    dirButtonShortEnable = false;
    if (!dirButtonLongEnable)
    {
        /* both button types disabled, thus disable interrupt */
        err = gpio_intr_disable(T_SW_PIN);    
    }
    return err;
}

/**
 * Hold direction button press.
 * 
 * A long hold of the direction button toggles nighttime mode.
 * 
 * @note This button registers after a duration of time has
 * passed with the direction button being held. Nothing happens
 * when the button is initially released afterward.
 */

esp_err_t enableHoldDirButton(void)
{
    esp_err_t err = ESP_OK;
    if ((!dirButtonShortEnable) && (!dirButtonLongEnable))
    {
        /* interrupt is disabled, thus enable it */
        dirButtonLongEnable = true;
        err = gpio_intr_enable(T_SW_PIN);
    } else
    {
        dirButtonLongEnable = true;
    }
    return err;
}

esp_err_t disableHoldDirButton(void)
{
    esp_err_t err = ESP_OK;
    dirButtonLongEnable = false;
    if (!dirButtonShortEnable)
    {
        /* both button types disabled, thus disable interrupt */
        err = gpio_intr_disable(T_SW_PIN);    
    }
    return err;
}

/**
 * OTA button press.
 * 
 * An OTA button press initiates an OTA update.
 * 
 * @note This button registers when the button is pressed,
 * not released, after a debouncing period.
 */

esp_err_t enableOTAButton(void)
{
    return gpio_intr_enable(IO_SW_PIN);
}

esp_err_t disableOTAButton(void)
{
    return gpio_intr_disable(IO_SW_PIN);
}

static esp_err_t initDirectionButton(void)
{
    /* The debounce timer is the timer that is set after the first ISR in a set of edges */
    const esp_timer_create_args_t debounceTimerArgs = {
        .name = "dirButtonDebounceTimer",
        .dispatch_method = ESP_TIMER_TASK,
        .callback = timerDebounceDirButtonCallback,
        .arg = NULL,
    };

    /* The hold timer is the timer that determines when a long button press registers */
    const esp_timer_create_args_t holdTimerArgs = {
        .name = "dirButtonHoldTimer",
        .dispatch_method = ESP_TIMER_TASK,
        .callback = timerDirButtonCallback,
        .arg = NULL,
    };
    esp_err_t err;

    /* initialize timers */
    err = esp_timer_create(&debounceTimerArgs, &dirButtonDebounceTimer); // lives forever
    if (err != ESP_OK) THROW_ERR(err);

    err = esp_timer_create(&holdTimerArgs, &dirButtonTimer); // lives forever
    if (err != ESP_OK) THROW_ERR(err);

    /* initialize direction button ISR */
    err = gpio_set_direction(T_SW_PIN, GPIO_MODE_INPUT);
    if (err != ESP_OK) THROW_ERR(err);
    err = gpio_set_intr_type(T_SW_PIN, GPIO_INTR_ANYEDGE);
    if (err != ESP_OK) THROW_ERR(err);
    err = gpio_isr_handler_add(T_SW_PIN, dirButtonISR, NULL);
    if (err != ESP_OK) THROW_ERR(err);

    return ESP_OK;
}

static esp_err_t initOTAButton(TaskHandle_t otaTask)
{
    esp_err_t err;

    err = gpio_set_pull_mode(IO_SW_PIN, GPIO_PULLUP_ONLY);
    if (err != ESP_OK) THROW_ERR(err);
    err = gpio_pullup_en(IO_SW_PIN);
    if (err != ESP_OK) THROW_ERR(err);
    err = gpio_set_direction(IO_SW_PIN, GPIO_MODE_INPUT);
    if (err != ESP_OK) THROW_ERR(err);
    err = gpio_set_intr_type(IO_SW_PIN, GPIO_INTR_NEGEDGE);
    if (err != ESP_OK) THROW_ERR(err);
    err = gpio_isr_handler_add(IO_SW_PIN, otaButtonISR, otaTask);
    if (err != ESP_OK) THROW_ERR(err);

    return ESP_OK;
}

/**
 * @brief Interrupt service routine that handles OTA button presses.
 * 
 * Handles OTA button presses to tell the main task to trigger an over-the-air
 * firmware upgrade.
 * 
 * @param params A TaskHandle_t that is the handle of the main task.
 */
static void otaButtonISR(void *params) {
    static TickType_t lastISRTick = 0;
    TaskHandle_t otaTask = (TaskHandle_t) params;
    TickType_t currentTick = xTaskGetTickCountFromISR();

    /* debounce button */
    if (currentTick - lastISRTick < pdMS_TO_TICKS(CONFIG_DEBOUNCE_PERIOD)) return;
    lastISRTick = currentTick;

    BaseType_t xHigherPriorityTaskWoken = pdFALSE;
    vTaskNotifyGiveFromISR(otaTask, &xHigherPriorityTaskWoken);
    portYIELD_FROM_ISR(xHigherPriorityTaskWoken);
}

/**
 * @brief Interrupt service routine that handles direction button presses.
 * 
 * @note The pin is active high, meaning a falling edge is expected before
 * a rising edge.
 */
static void dirButtonISR(void *params)
{
    /* debounce button. Set a timer and don't interrupt during debounce period */
    (void) gpio_intr_disable(T_SW_PIN); // nowhere for error to go
    (void) esp_timer_start_once(dirButtonDebounceTimer, 50 * 1000); // 100ms debounce period, nowhere for error to go
}

/**
 * Callback for when the direction button timer expires. This
 * indicates that the button has been held long enough for the
 * input to be considered a long/hold button press.
 * 
 * @note If hold dir button presses are disabled, this is
 * interpreted as a short button press.
 * 
 * @param params NULL
 */
static void timerDirButtonCallback(void *params)
{
    MainCommand cmd = MAIN_CMD_HOLD_DIR_BTN;
    if (!dirButtonLongEnable) return;

    (void) xQueueSend(inputQueue, &cmd, portMAX_DELAY); // nowhere to send error
}

/**
 * Callback for when the direction button debounce timer expires. This timer
 * is set when the first edge is detected and expires when the line has settled
 * to the point where reading the output of the line is deterministic.
 * 
 * @param params NULL
 */
static void timerDebounceDirButtonCallback(void *params)
{
    static bool prevRising = false; // whether the previous button press was rising or falling. These are expected
                                    // in sequence, so any duplicates are rejected. Duplicates are either line glitches
                                    // or the user is spamming the button, in which case only the first press should count.

    MainCommand cmd = MAIN_CMD_QUICK_DIR_BTN;
    bool rising = (gpio_get_level(T_SW_PIN) == 0) ? true : false;

    /* handle button edges */
    if (rising && !prevRising)
    { // rising edge
        ESP_EARLY_LOGI(TAG, "rising");
         /* set timer and register short button press */
        (void) esp_timer_start_once(dirButtonTimer, DIR_BUTTON_LONG_PRESS_TIME_US); // nowhere for error to go
        incrementAbortCount();
        (void) xQueueSend(inputQueue, &cmd, portMAX_DELAY); // nowhere to send error
        prevRising = true;
    } else if (!rising && prevRising)
    { // falling edge
        ESP_EARLY_LOGI(TAG, "falling");
        /* stop timer */
        (void) esp_timer_stop(dirButtonTimer); // just need it to stop
                                               // Note that there is a known race condition here.
                                               // If the user is spamming the button, the timer might
                                               // never be stopped as is normal because falling edges
                                               // might not be detected an incredibly rare number of times.
                                               // This behavior is preferrable to always stopping the
                                               // timer because that might cause slightly more noticeable
                                               // issues if the line is glitchy where a long button press
                                               // is detected when it shouldn't be. I consider this the lesser
                                               // of two evils because it is exceedingly rare if a long button
                                               // press is sufficiently long.
        prevRising = false;
    }

    (void) gpio_intr_enable(T_SW_PIN);
}
