zinkwazi/traffic-pcb-sb/software/esp-firmware/components/led_matrix/src/V2_0_led_registers.c

/**
 * V2_0_led_registers.c
 * 
 * Cointains LED number to matrix register mappings for V2_0 of the hardware.
 */

#include "sdkconfig.h"

#if CONFIG_HARDWARE_VERSION == 2

#include "led_registers.h"

#include <stdint.h>

#include "led_types.h"

/* A mapping from LED number to corresponding 
matrix registers for each color (red, green, blue),
where index (i - 1) corresponds to LED number i. */
const LEDReg LEDNumToReg[MAX_NUM_LEDS_REG] = {
    {0x8D, 0x8F, 0x8E, MAT1_PAGE1}, // 1
    {0x96, 0x98, 0x97, MAT1_PAGE1}, // 2
    {0x9F, 0xA1, 0xA0, MAT1_PAGE1}, // 3
    {0xA8, 0xAA, 0xA9, MAT1_PAGE1}, // 4
    {0x84, 0x86, 0x85, MAT1_PAGE1}, // 5
    {0x7B, 0x7D, 0x7C, MAT1_PAGE1}, // 6
    {0x72, 0x74, 0x73, MAT1_PAGE1}, // 7
    {0x69, 0x6B, 0x6A, MAT1_PAGE1}, // 8
    {0x60, 0x62, 0x61, MAT1_PAGE1}, // 9
    {0x8A, 0x8C, 0x8B, MAT1_PAGE1}, // 10
    {0x93, 0x95, 0x94, MAT1_PAGE1}, // 11
    {0x9C, 0x9E, 0x9D, MAT1_PAGE1}, // 12
    {0xA5, 0xA7, 0xA6, MAT1_PAGE1}, // 13
    {0x81, 0x83, 0x82, MAT1_PAGE1}, // 14
    {0x78, 0x7A, 0x79, MAT1_PAGE1}, // 15
    {0x6F, 0x71, 0x70, MAT1_PAGE1}, // 16
    {0x66, 0x68, 0x67, MAT1_PAGE1}, // 17
    {0x5D, 0x5F, 0x5E, MAT1_PAGE1}, // 18
    {0x87, 0x88, 0x89, MAT1_PAGE1}, // 19
    {0x90, 0x91, 0x92, MAT1_PAGE1}, // 20
    {0x99, 0x9A, 0x9B, MAT1_PAGE1}, // 21
    {0xA2, 0xA3, 0xA4, MAT1_PAGE1}, // 22
    {0x7E, 0x7F, 0x80, MAT1_PAGE1}, // 23
    {0x75, 0x76, 0x77, MAT1_PAGE1}, // 24
    {0x6C, 0x6D, 0x6E, MAT1_PAGE1}, // 25
    {0x63, 0x64, 0x65, MAT1_PAGE1}, // 26
    {0x5A, 0x5B, 0x5C, MAT1_PAGE1}, // 27
    {0xB1, 0xB2, 0xB3, MAT1_PAGE0}, // 28
    {0x1B, 0x1C, 0x1D, MAT1_PAGE1}, // 29
    {0x39, 0x3A, 0x3B, MAT1_PAGE1}, // 30
    {0x57, 0x58, 0x59, MAT1_PAGE1}, // 31
    {0x93, 0x94, 0x95, MAT1_PAGE0}, // 32
    {0x75, 0x76, 0x77, MAT1_PAGE0}, // 33
    {0x57, 0x58, 0x59, MAT1_PAGE0}, // 34
    {0x39, 0x3A, 0x3B, MAT1_PAGE0}, // 35
    {0x1B, 0x1C, 0x1D, MAT1_PAGE0}, // 36
    {0xAE, 0xAF, 0xB0, MAT1_PAGE0}, // 37
    {0x18, 0x19, 0x1A, MAT1_PAGE1}, // 38
    {0x36, 0x37, 0x38, MAT1_PAGE1}, // 39
    {0x54, 0x55, 0x56, MAT1_PAGE1}, // 40
    {0x90, 0x91, 0x92, MAT1_PAGE0}, // 41
    {0x72, 0x73, 0x74, MAT1_PAGE0}, // 42
    {0x54, 0x55, 0x56, MAT1_PAGE0}, // 43
    {0x36, 0x37, 0x38, MAT1_PAGE0}, // 44
    {0x18, 0x19, 0x1A, MAT1_PAGE0}, // 45
    {0xFF, 0xFF, 0xFF, MAT_NONE}, // 46, removed from V2_0
    {0x96, 0x98, 0x97, MAT4_PAGE1}, // 47
    {0x9F, 0xA1, 0xA0, MAT4_PAGE1}, // 48
    {0xA8, 0xAA, 0xA9, MAT4_PAGE1}, // 49
    {0x84, 0x86, 0x85, MAT4_PAGE1}, // 50
    {0x7B, 0x7D, 0x7C, MAT4_PAGE1}, // 51
    {0x72, 0x74, 0x73, MAT4_PAGE1}, // 52
    {0x69, 0x6B, 0x6A, MAT4_PAGE1}, // 53
    {0x60, 0x62, 0x61, MAT4_PAGE1}, // 54
    {0xAB, 0xAC, 0xAD, MAT1_PAGE0}, // 55
    {0x15, 0x16, 0x17, MAT1_PAGE1}, // 56
    {0x33, 0x34, 0x35, MAT1_PAGE1}, // 57
    {0x51, 0x52, 0x53, MAT1_PAGE1}, // 58
    {0x8D, 0x8E, 0x8F, MAT1_PAGE0}, // 59
    {0x6F, 0x70, 0x71, MAT1_PAGE0}, // 60
    {0x51, 0x52, 0x53, MAT1_PAGE0}, // 61
    {0x33, 0x34, 0x35, MAT1_PAGE0}, // 62
    {0x15, 0x16, 0x17, MAT1_PAGE0}, // 63
    {0x8A, 0x8C, 0x8B, MAT4_PAGE1}, // 64
    {0x93, 0x95, 0x94, MAT4_PAGE1}, // 65
    {0x9C, 0x9E, 0x9D, MAT4_PAGE1}, // 66
    {0xA5, 0xA7, 0xA6, MAT4_PAGE1}, // 67
    {0x81, 0x83, 0x82, MAT4_PAGE1}, // 68
    {0x78, 0x7A, 0x79, MAT4_PAGE1}, // 69
    {0x6F, 0x71, 0x70, MAT4_PAGE1}, // 70
    {0x66, 0x68, 0x67, MAT4_PAGE1}, // 71
    {0x5D, 0x5F, 0x5E, MAT4_PAGE1}, // 72
    {0xA8, 0xAA, 0xA9, MAT1_PAGE0}, // 73
    {0x12, 0x14, 0x13, MAT1_PAGE1}, // 74
    {0x30, 0x32, 0x31, MAT1_PAGE1}, // 75
    {0x4E, 0x50, 0x4F, MAT1_PAGE1}, // 76
    {0x8A, 0x8C, 0x8B, MAT1_PAGE0}, // 77
    {0x6C, 0x6E, 0x6D, MAT1_PAGE0}, // 78
    {0x4E, 0x50, 0x4F, MAT1_PAGE0}, // 79
    {0x30, 0x32, 0x31, MAT1_PAGE0}, // 80
    {0x12, 0x14, 0x13, MAT1_PAGE0}, // 81
    {0xA2, 0xA3, 0xA4, MAT1_PAGE0}, // 82
    {0x0C, 0x0D, 0x0E, MAT1_PAGE1}, // 83
    {0x2A, 0x2B, 0x2C, MAT1_PAGE1}, // 84
    {0x48, 0x49, 0x4A, MAT1_PAGE1}, // 85
    {0x84, 0x85, 0x86, MAT1_PAGE0}, // 86
    {0x66, 0x67, 0x68, MAT1_PAGE0}, // 87
    {0x48, 0x49, 0x4A, MAT1_PAGE0}, // 88
    {0x2A, 0x2B, 0x2C, MAT1_PAGE0}, // 89
    {0x0C, 0x0D, 0x0E, MAT1_PAGE0}, // 90
    {0xAB, 0xAC, 0xAD, MAT4_PAGE0}, // 91
    {0x15, 0x16, 0x17, MAT4_PAGE1}, // 92
    {0x33, 0x34, 0x35, MAT4_PAGE1}, // 93
    {0x51, 0x52, 0x53, MAT4_PAGE1}, // 94
    {0x8D, 0x8E, 0x8F, MAT4_PAGE0}, // 95
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
    {0x09, 0x0A, 0x0B, MAT4_PAGE0}, // 401
    {0x96, 0x97, 0x98, MAT4_PAGE0}, // 402
    {0x00, 0x01, 0x02, MAT4_PAGE1}, // 403
    {0x1E, 0x1F, 0x20, MAT4_PAGE1}, // 404
    {0x3C, 0x3D, 0x3E, MAT4_PAGE1}, // 405
    {0x78, 0x79, 0x7A, MAT4_PAGE0}, // 406
    {0x5A, 0x5B, 0x5C, MAT4_PAGE0}, // 407
    {0x3C, 0x3D, 0x3E, MAT4_PAGE0}, // 408
    {0x9F, 0xA0, 0xA1, MAT1_PAGE0}, // 409
    {0x09, 0x0A, 0x0B, MAT1_PAGE1}, // 410
    {0x27, 0x28, 0x29, MAT1_PAGE1}, // 411
    {0x45, 0x46, 0x47, MAT1_PAGE1}, // 412
    {0x81, 0x82, 0x83, MAT1_PAGE0}, // 413
    {0x03, 0x04, 0x05, MAT1_PAGE0}, // 414
};

#endif /* CONFIG_HARDWARE_VERISON == 2 */
 
