zinkwazi/traffic-pcb-sb/software/esp-firmware/components/animations/src/V2_0_led_coordinates.c

/**
 * V2_0_led_coordinates.c
 * 
 * Contains the Kicad coordinates of each LED on V2_0 of the board, where (0, 0)
 * is the center of the board, increasing X is to the right, and increasing Y
 * is to the bottom.
 */
#include "sdkconfig.h"

#if CONFIG_HARDWARE_VERSION == 2

#include "led_coordinates.h"

#include <stdint.h>

#include "animation_types.h"


/* A mapping from LED number to x, y PCB coordinates,
where index (i - 1) corresponds to LED number i. */
const LEDCoord LEDNumToCoord[ANIM_STANDARD_ARRAY_SIZE] = {
	{-178, 68}, // 1
	{-175, 66}, // 2
	{-171, 65}, // 3
	{-167, 64}, // 4
	{-164, 64}, // 5
	{-160, 64}, // 6
	{-156, 65}, // 7
	{-152, 65}, // 8
	{-148, 65}, // 9
	{-144, 65}, // 10
	{-140, 64}, // 11
	{-137, 62}, // 12
	{-133, 60}, // 13
	{-130, 61}, // 14
	{-126, 61}, // 15
	{-122, 61}, // 16
	{-119, 61}, // 17
	{-115, 61}, // 18
	{-111, 60}, // 19
	{-107, 59}, // 20
	{-104, 58}, // 21
	{-100, 56}, // 22
	{-97, 54}, // 23
	{-94, 52}, // 24
	{-90, 51}, // 25
	{-88, 48}, // 26
	{-85, 46}, // 27
	{-82, 43}, // 28
	{-79, 40}, // 29
	{-75, 40}, // 30
	{-72, 37}, // 31
	{-70, 34}, // 32
	{-66, 32}, // 33
	{-62, 31}, // 34
	{-59, 30}, // 35
	{-56, 28}, // 36
	{-52, 28}, // 37
	{-49, 26}, // 38
	{-45, 24}, // 39
	{-42, 22}, // 40
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
	{0, 0}, // there is no LED with number 46
	{-37, 31}, // 47
	{-33, 29}, // 48
	{-30, 28}, // 49
	{-26, 29}, // 50
	{-22, 29}, // 51
	{-19, 29}, // 52
	{-15, 29}, // 53
	{-11, 29}, // 54
	{-37, 17}, // 55
	{-37, 14}, // 56
	{-37, 10}, // 57
	{-35, 7}, // 58
	{-31, 4}, // 59
	{-29, 1}, // 60
	{-27, -2}, // 61
	{-26, -6}, // 62
	{-22, -8}, // 63
	{-7, 29}, // 64
	{-3, 30}, // 65
	{1, 32}, // 66
	{5, 32}, // 67
	{9, 32}, // 68
	{11, 34}, // 69
	{15, 35}, // 70
	{19, 34}, // 71
	{23, 33}, // 72
	{-19, 19}, // 73
	{-15, 19}, // 74
	{-11, 17}, // 75
	{-8, 16}, // 76
	{-4, 14}, // 77
	{-1, 12}, // 78
	{3, 12}, // 79
	{7, 11}, // 80
	{11, 11}, // 81
	{-19, -9}, // 82
	{-16, -11}, // 83
	{-12, -12}, // 84
	{-8, -13}, // 85
	{-5, -15}, // 86
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
};

#endif /* CONFIG_HARDWARE_VERSION == 2*/
