zinkwazi/traffic-pcb-sb/software/esp-firmware/main/include/wifi.h

/**
 * wifi.h
 * 
 * Contains functions that manage wifi events.
 */

#ifndef WIFI_H_
#define WIFI_H_

#include <stdbool.h>

#include "esp_err.h"

esp_err_t initWifi(char *wifiSSID, char* wifiPass);
bool isWifiConnected(void);
esp_err_t establishWifiConnection(void);
esp_err_t unregisterWifiHandler(void); // used in OTA task before restart

#endif /* WIFI_H_ */
