zinkwazi/traffic-pcb-sb/software/esp-firmware/components/animations/include/animation_types.h

/**
 * animation_types.h
 * 
 * Contains types necessary for animation logic.
 */

#ifndef ANIMATION_TYPES_H_
#define ANIMATION_TYPES_H_

#include <stdint.h>

struct LEDCoord {
    int32_t x;
    int32_t y;
};

typedef struct LEDCoord LEDCoord;

#endif /* ANIMATION_TYPES_H_ */
